gzalles/ambisonics-z-array/cad/dl/screws/M2_Screw_Attempt__3_for_T732_912171/README.txt

M2 Screw Attempt #3 for T732 by Zohan on Thingiverse: https://www.thingiverse.com/thing:912171
