gzalles/ambisonics-z-array/cad/dl/screws/M3_SCREW_WITH_NUT_3730355/README.txt

M3 SCREW WITH NUT by Fern528 on Thingiverse: https://www.thingiverse.com/thing:3730355
