gzalles/ambisonics-z-array/pcb/MEMS_quart_board/40720/3_175mm-radius/misc/full/README.md

this is the gerber files that pcbway made from the .brd file that CM gave me. 
it is a more complete view of the single mems board with 3.175 mm radius
