gzalles/ambisonics-z-array/cad/bigSpHEAR_mems/angles.png

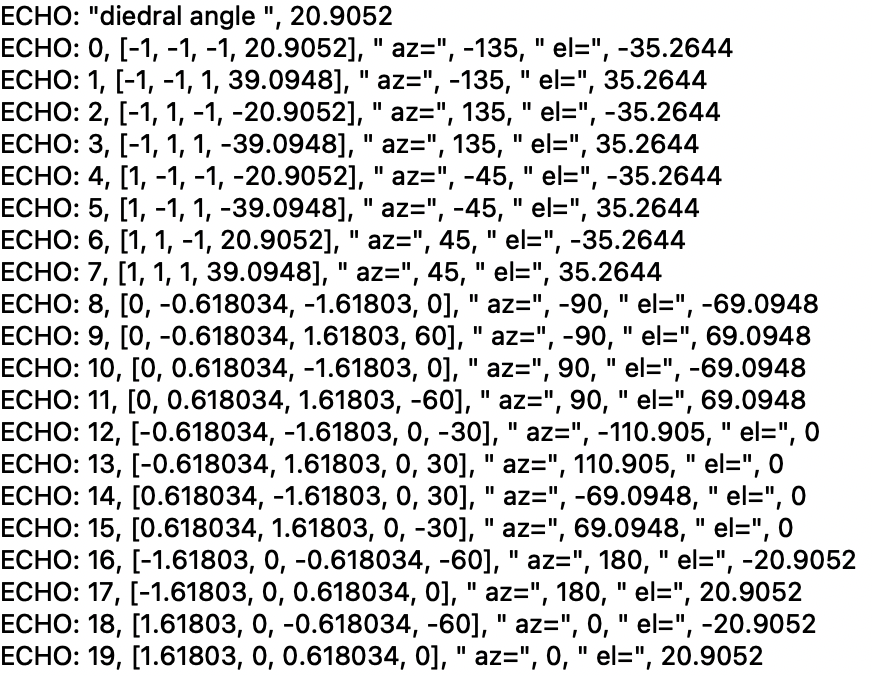
cad/bigSpHEAR_mems/angles.png
