gzalles/ambisonics-z-array/cad/dl/mic-holder/images/Mic_Holder_Samson_Q2U.JPG

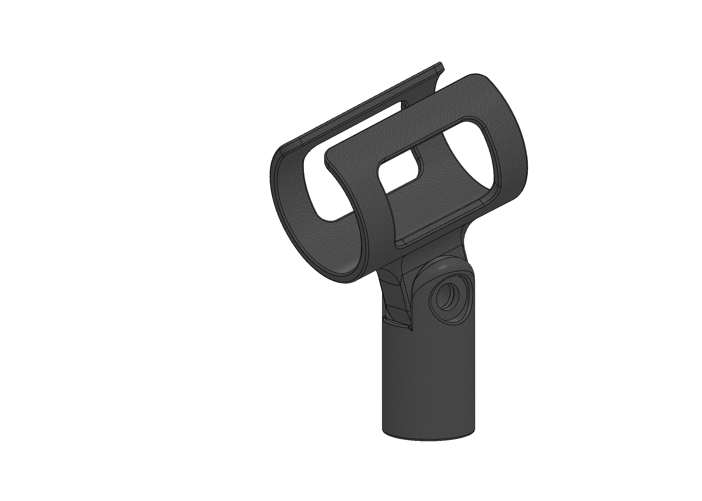
cad/dl/mic-holder/images/Mic_Holder_Samson_Q2U.JPG
