gzalles/ambisonics-z-array/cad/dl/screws/M3_SCREW_WITH_NUT_3730355/images/Capture.JPG

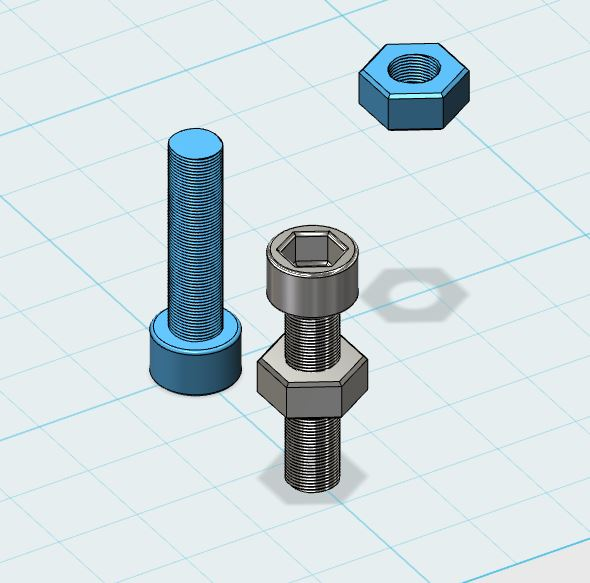
cad/dl/screws/M3_SCREW_WITH_NUT_3730355/images/Capture.JPG
