gzalles/ambisonics-z-array/cad/octo/_angles.png

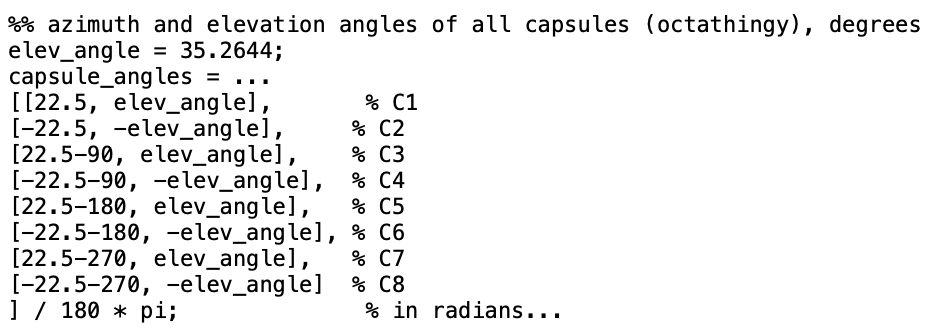
cad/octo/_angles.png
