gzalles/ambisonics-z-array/cad/octo/mch/prusa.png

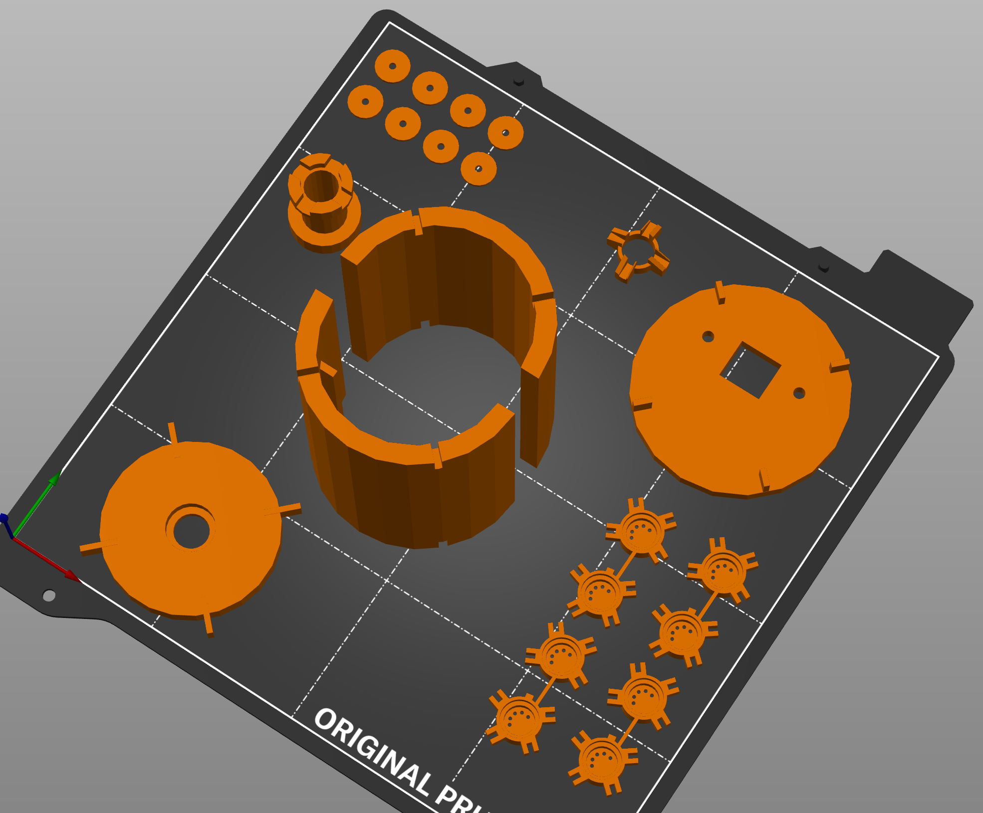
cad/octo/mch/prusa.png
