gzalles/ambisonics-z-array/m/eps/D1/D1-DFRs-AF-local-EQ.jpeg

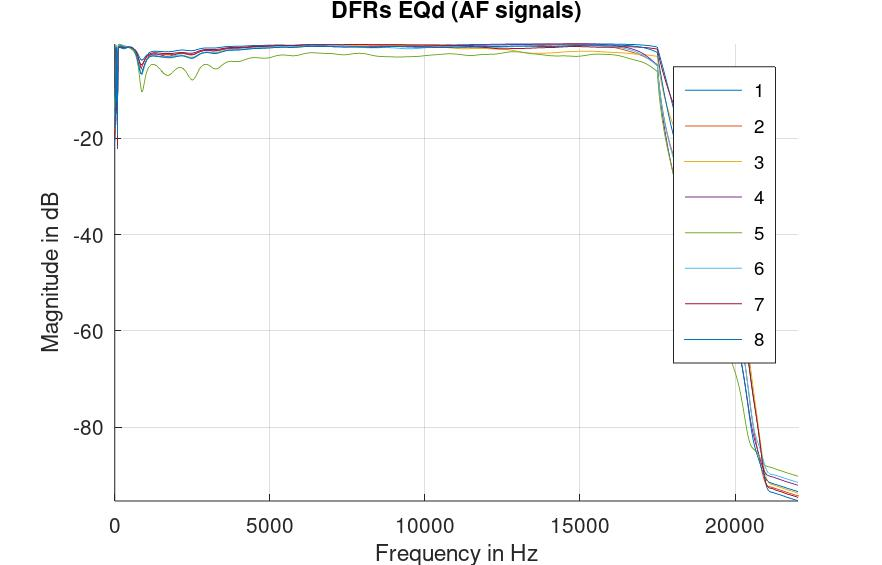
m/eps/D1/D1-DFRs-AF-local-EQ.jpeg
