gzalles/ambisonics-z-array/m/eps/D1/D1-on-axis-preAF-EQ.jpeg

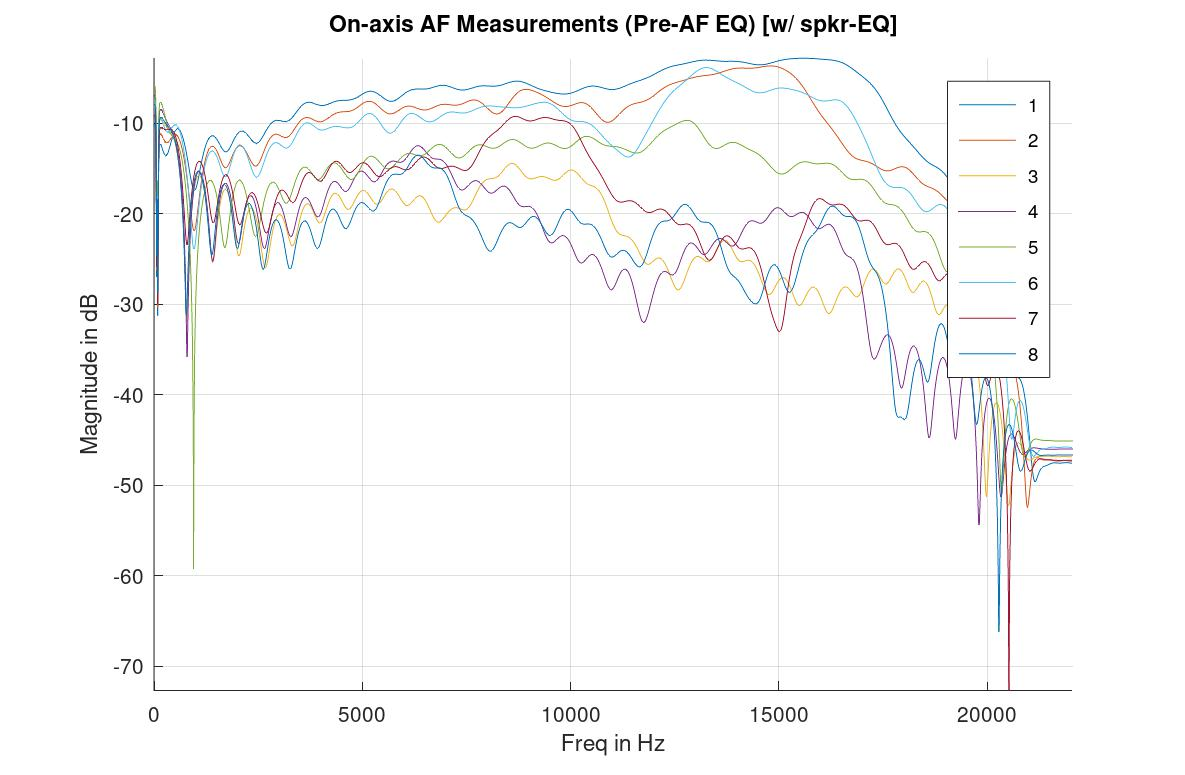
m/eps/D1/D1-on-axis-preAF-EQ.jpeg
