gzalles/ambisonics-z-array/m/eps/D1/D1-SH1-EQ-DFR.jpeg

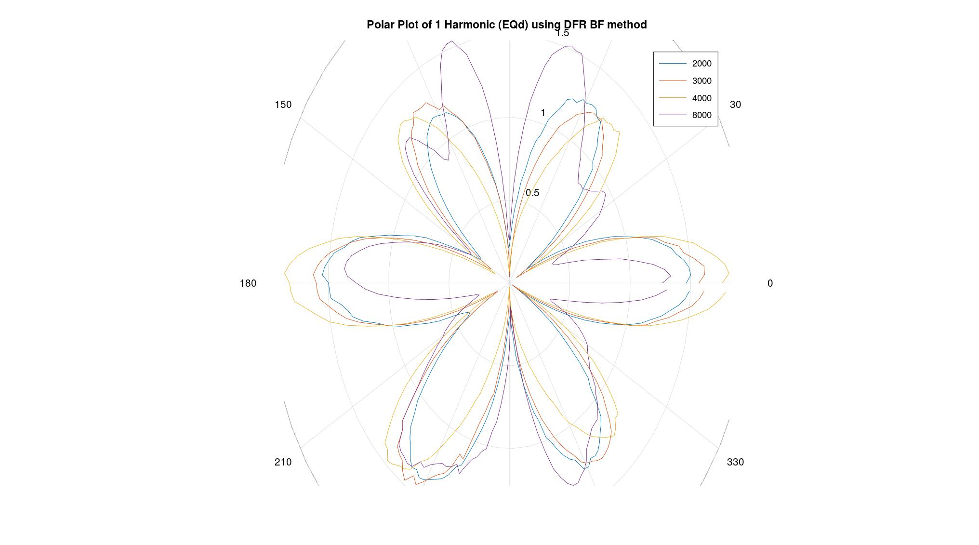
m/eps/D1/D1-SH1-EQ-DFR.jpeg
