gzalles/ambisonics-z-array/m/eps/D1/D1-SH-BF-EQ-peak.jpeg

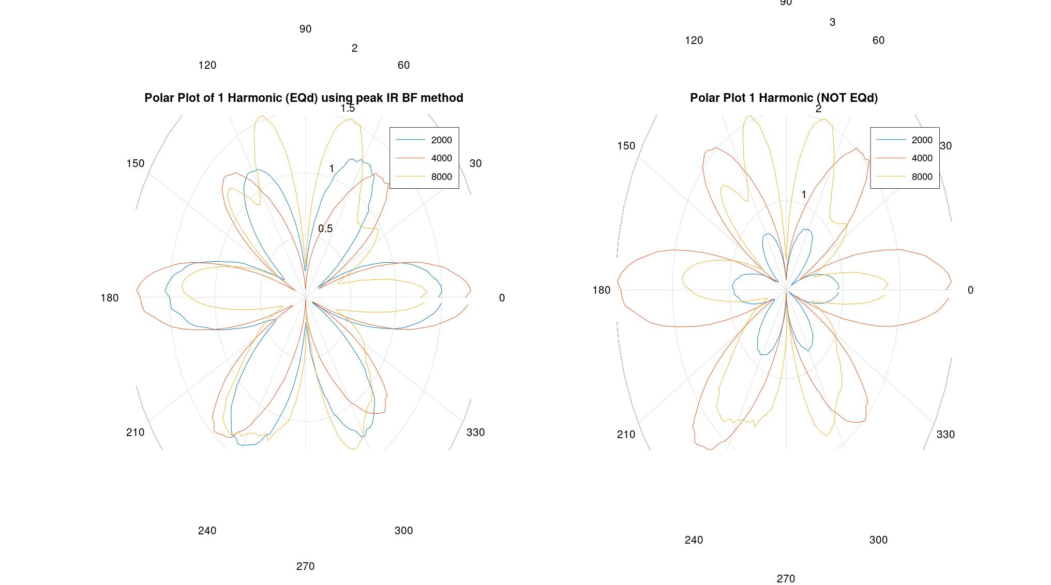
m/eps/D1/D1-SH-BF-EQ-peak.jpeg
