gzalles/ambisonics-z-array/m/eps/D1/D1-SHs-ALL-2k.jpeg

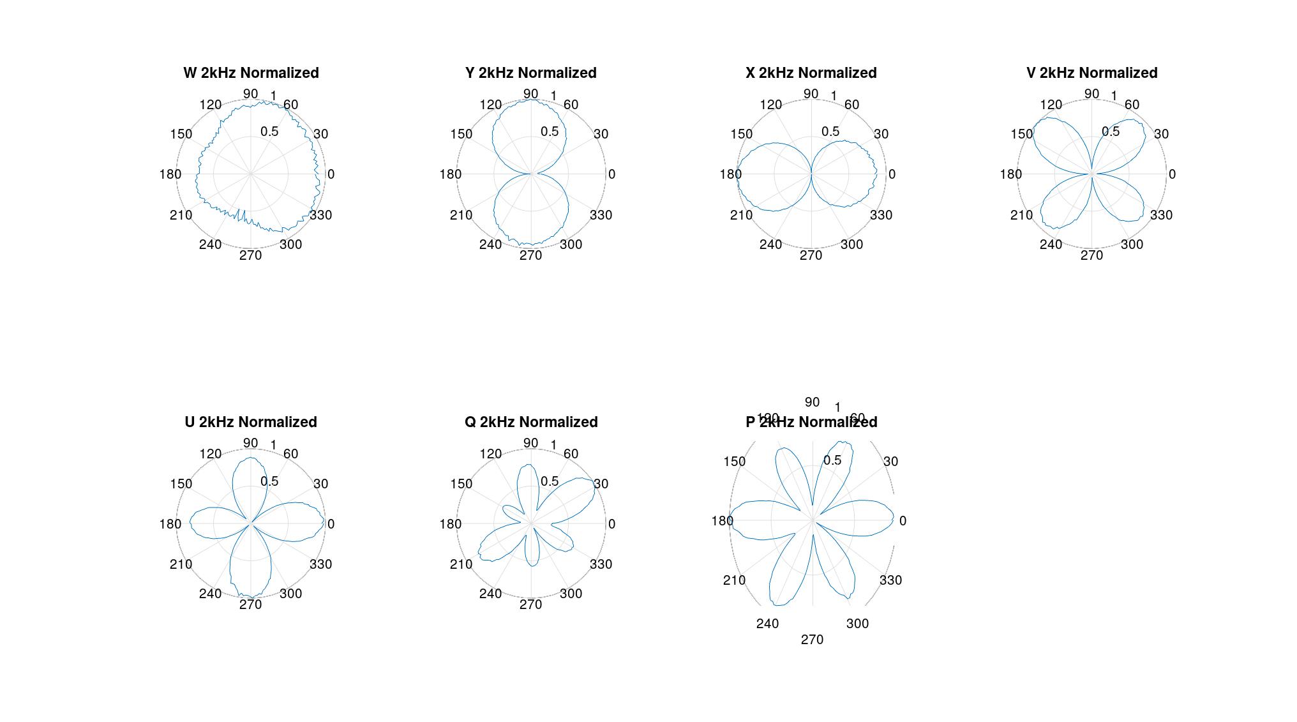
m/eps/D1/D1-SHs-ALL-2k.jpeg
