gzalles/ambisonics-z-array/m/eps/D2/D2-1st-IR-AF-P1-EQ.jpeg

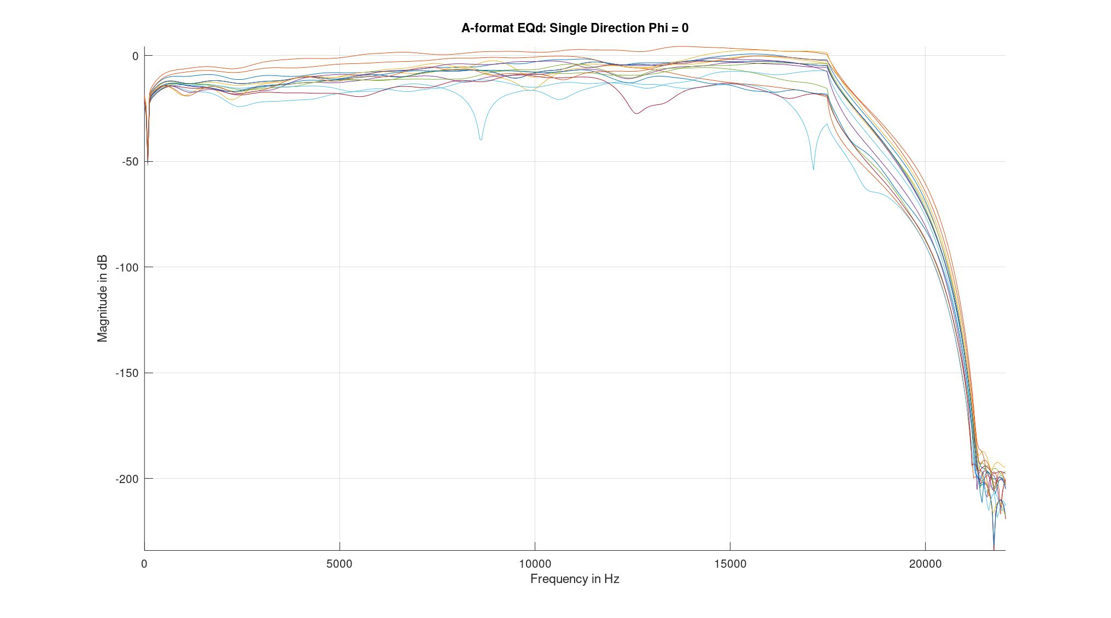
m/eps/D2/D2-1st-IR-AF-P1-EQ.jpeg
