gzalles/ambisonics-z-array/m/eps/D2/D2-SH-ALL-3K.jpeg

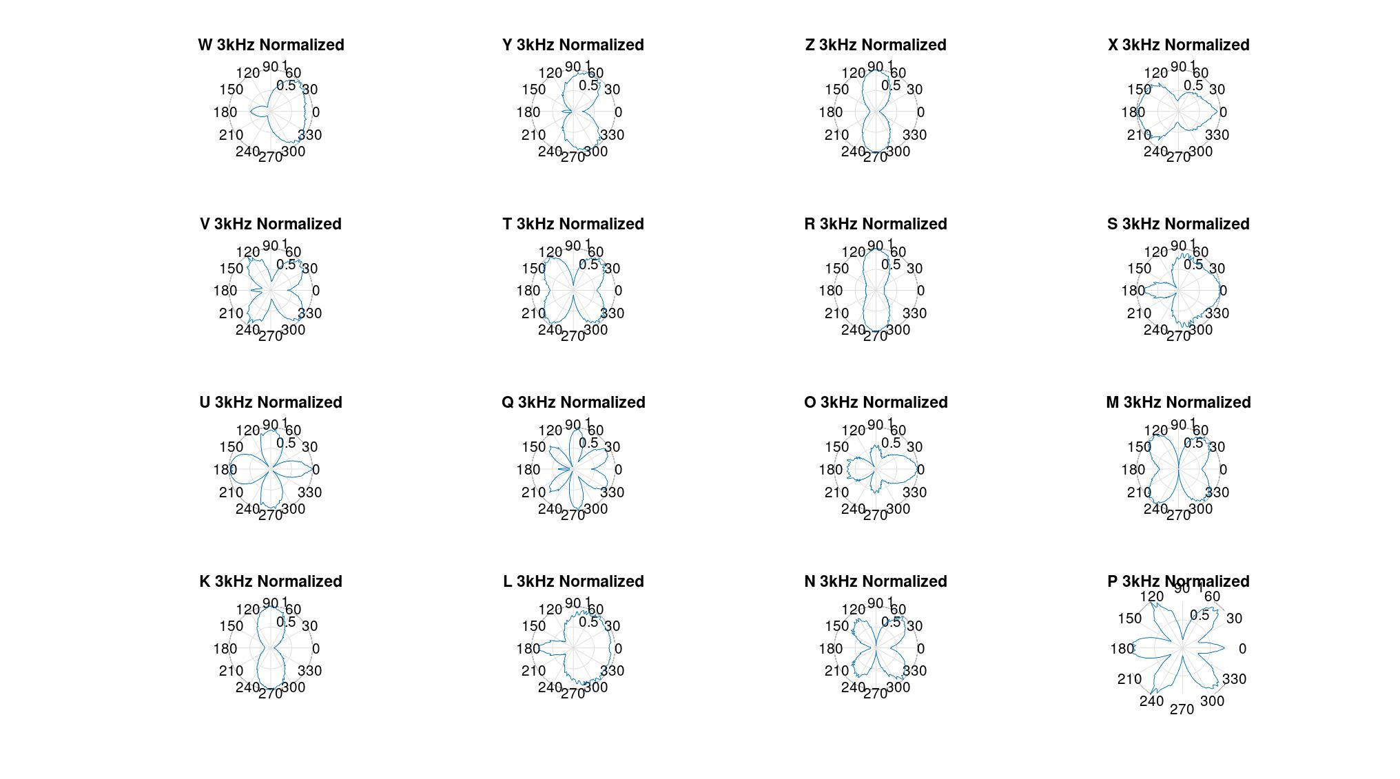
m/eps/D2/D2-SH-ALL-3K.jpeg
