gzalles/ambisonics-z-array/m/eps/D2/D2-SH-ALL-EQ-DFR.jpeg

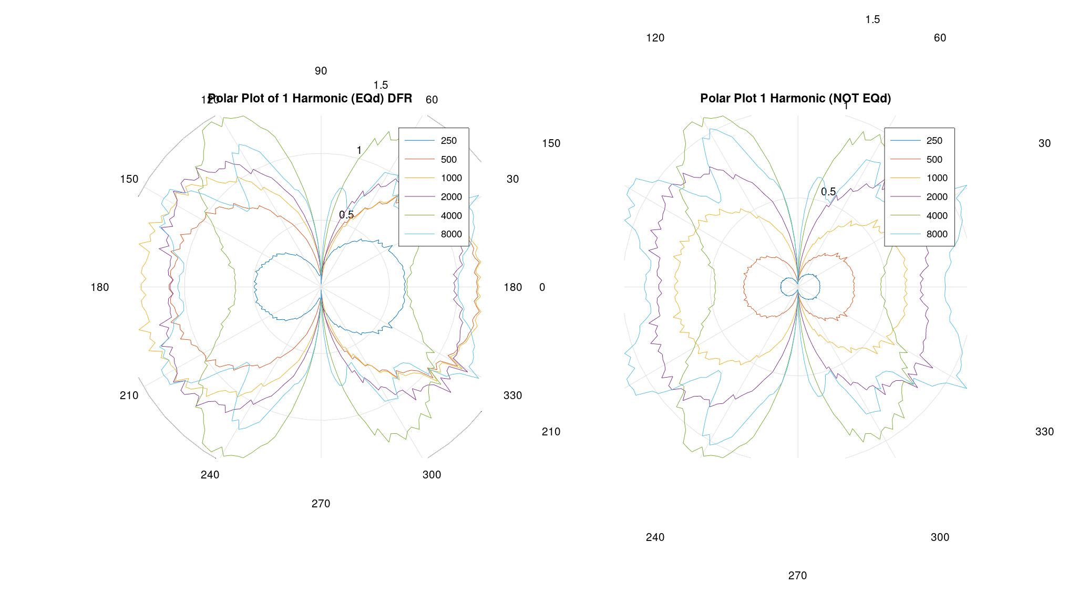
m/eps/D2/D2-SH-ALL-EQ-DFR.jpeg
