gzalles/ambisonics-z-array/pcb/ICS-41350-PDM-Mic-master/dimensions.png

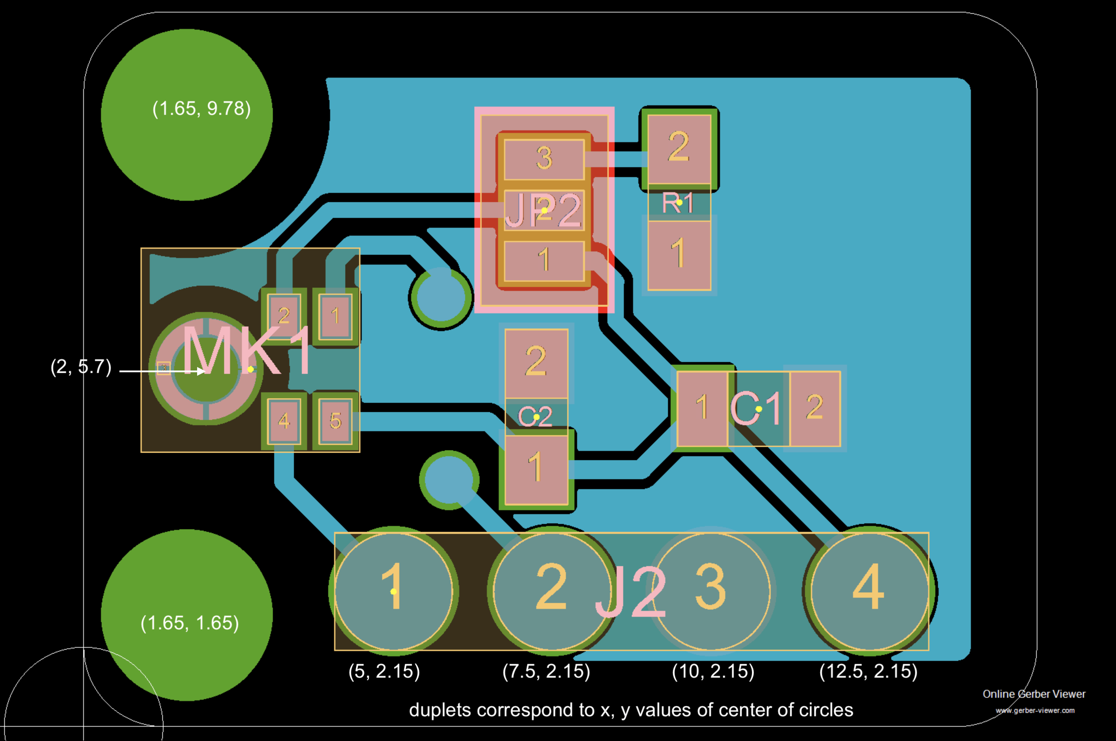
pcb/ICS-41350-PDM-Mic-master/dimensions.png
