gzalles/ambisonics-z-array/pcb/MEMS_quart_board/43432/gerber.png

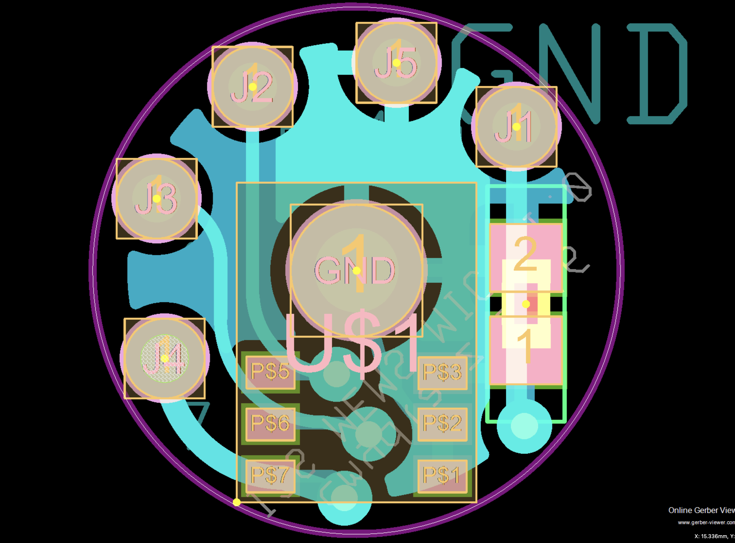
pcb/MEMS_quart_board/43432/gerber.png
