gzalles/ambisonics-z-array/pcb/MEMS_quart_board/43434/gerber2.png

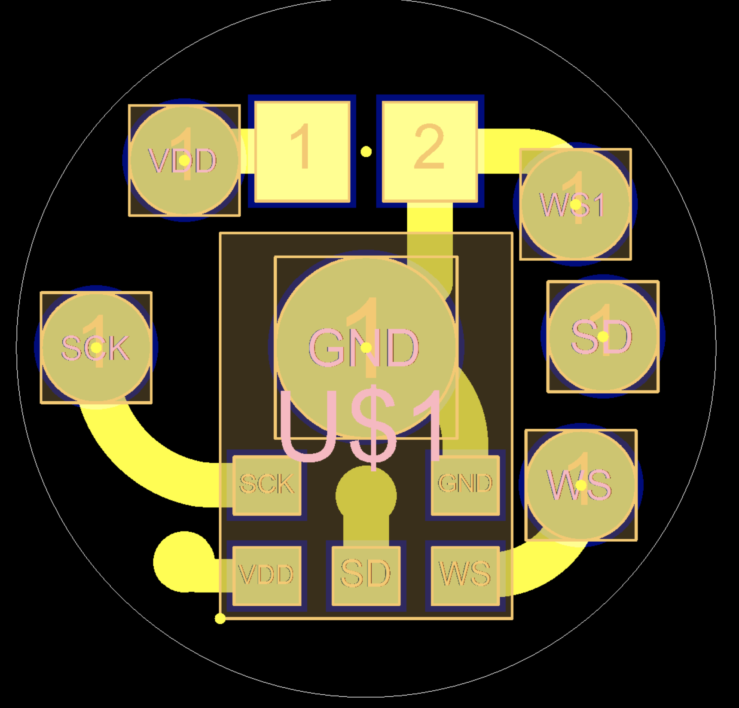
pcb/MEMS_quart_board/43434/gerber2.png
