gzalles/ambisonics-z-array/pcb/MEMS_quart_board/52000/tdm52000-circuit/example1.png

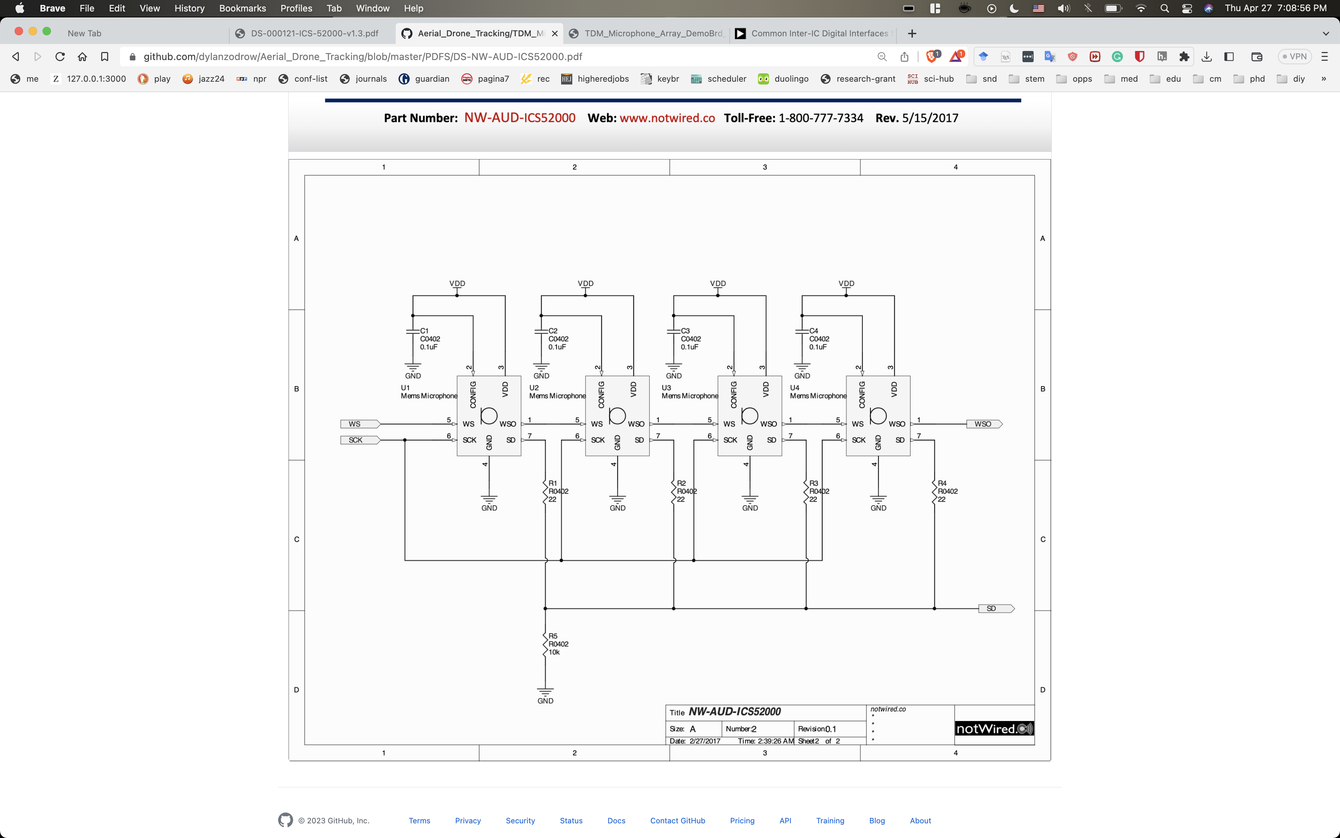
pcb/MEMS_quart_board/52000/tdm52000-circuit/example1.png
