gzalles/ambisonics-z-array/pcb/MEMS_quart_board/SPH0645LM4H/F-RES.png

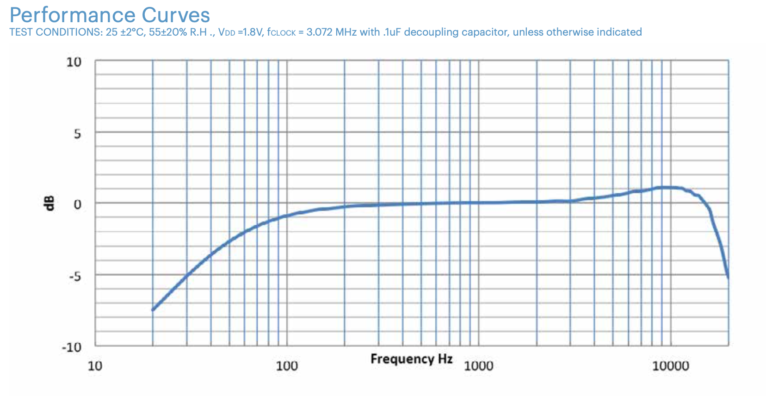
pcb/MEMS_quart_board/SPH0645LM4H/F-RES.png
