gzalles/ambisonics-z-array/cad/dl/scad/gzb/tetrahedron.stl

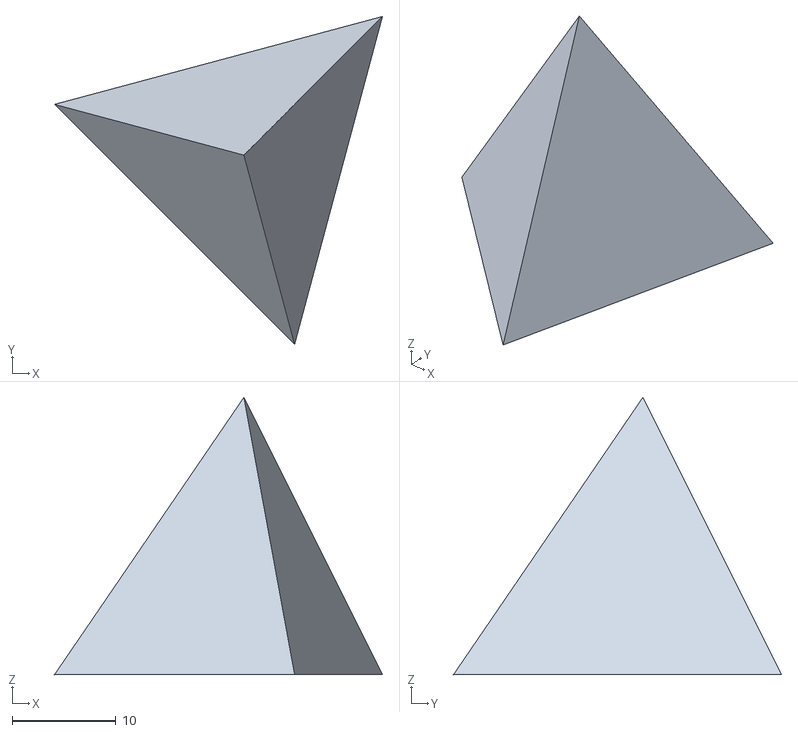
[picture p46: CAD file, 2023-04-07]
cad/dl/scad/gzb/tetrahedron.stl
31.5 x 31.5 x 26.7
