gzalles/ambisonics-z-array/cad/gzb.stl

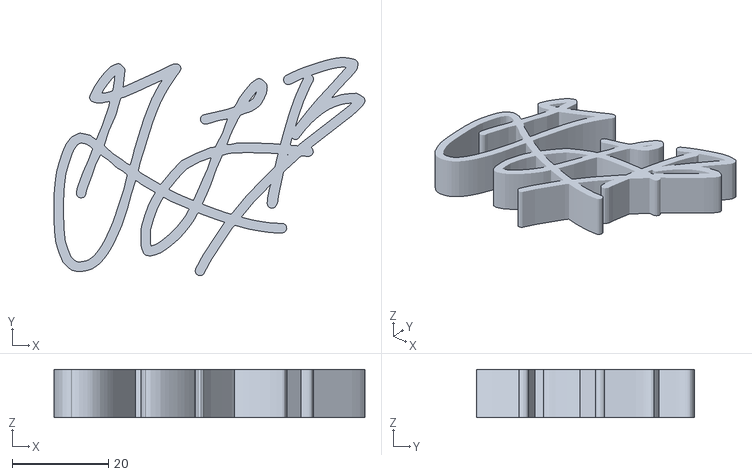
[picture p47: CAD file, 2023-05-23]
cad/gzb.stl
64.6 x 45.3 x 10.0
