gzalles/ambisonics-z-array/cad/max360/83/v2/top.stl

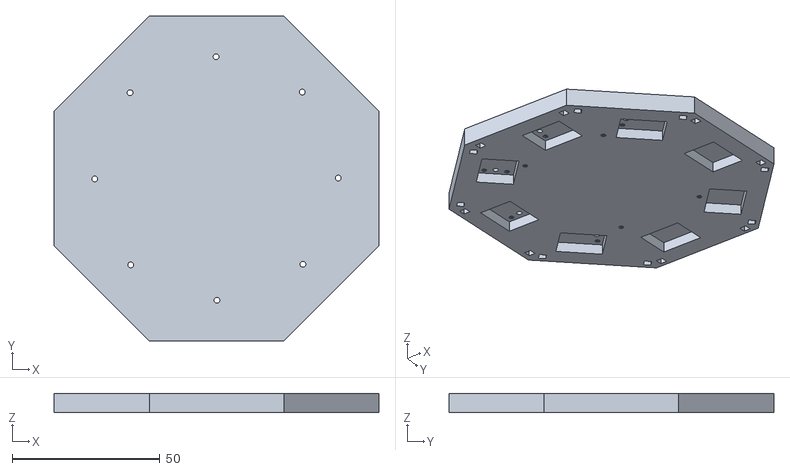
[picture p48: CAD file, 2023-04-07]
cad/max360/83/v2/top.stl
109.9 x 109.9 x 6.59
