gzalles/ambisonics-z-array/cad/max360/ada/2D-I2S-8CH/bottom.3mf

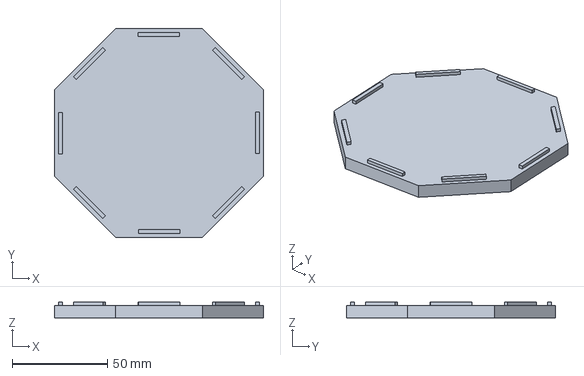
[picture p49: CAD file, 2023-04-07]
cad/max360/ada/2D-I2S-8CH/bottom.3mf
110.0 x 110.0 x 8.24 mm
