gzalles/ambisonics-z-array/cad/max360/ada/2D-I2S-8CH/stl/sides_x7.stl

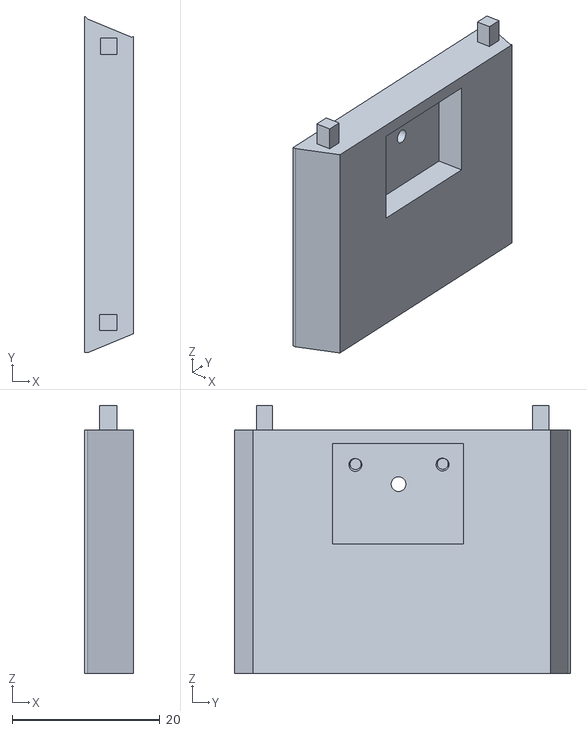
[picture p50: CAD file, 2023-04-07]
cad/max360/ada/2D-I2S-8CH/stl/sides_x7.stl
6.59 x 45.5 x 36.2
