gzalles/ambisonics-z-array/cad/max360/ada/3D-PDM-16CH/sides.3mf

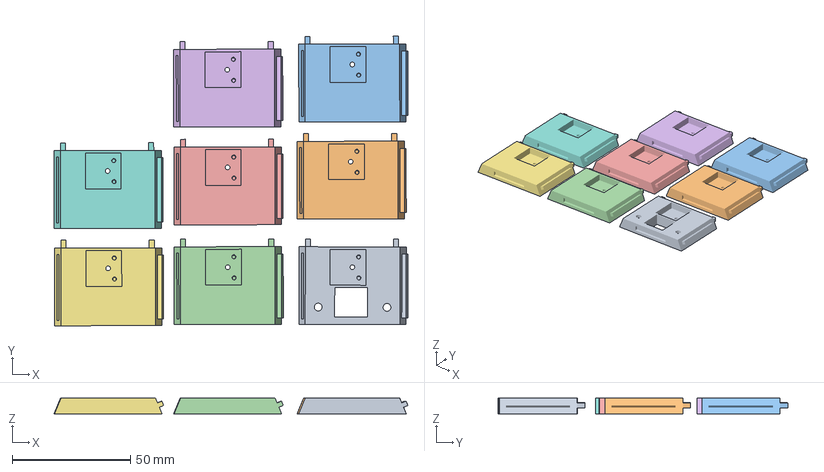
[picture p51: CAD file, 2023-04-07]
cad/max360/ada/3D-PDM-16CH/sides.3mf
149.9 x 122.6 x 6.59 mm
sideA.stl
sideB.stl x 7
