gzalles/ambisonics-z-array/cad/max360/ada/3D-PDM-16CH/stl/sideA.stl

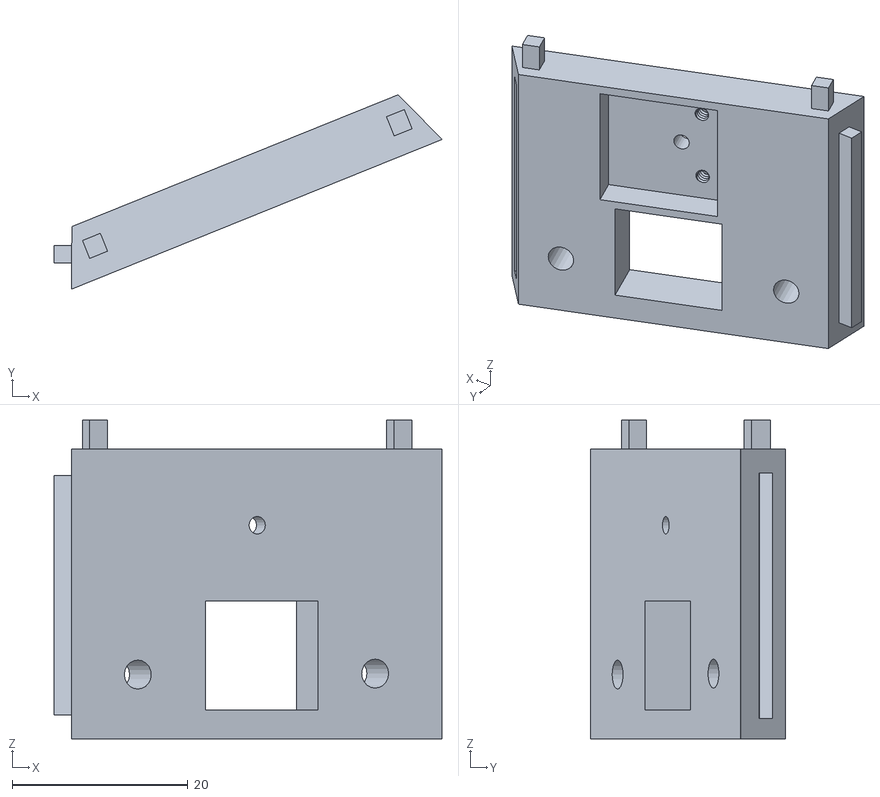
[picture p52: CAD file, 2023-04-07]
cad/max360/ada/3D-PDM-16CH/stl/sideA.stl
44.1 x 22.1 x 36.2
