gzalles/ambisonics-z-array/cad/msma-mch/capHolder16-new.3mf

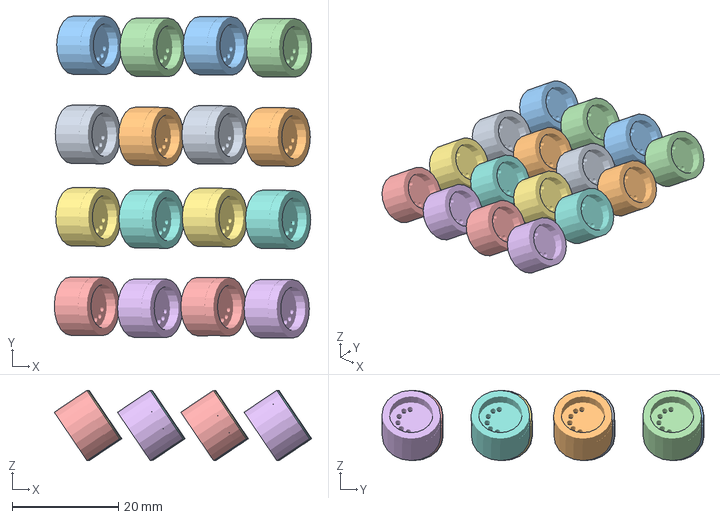
[picture p53: CAD file, 2023-04-19]
cad/msma-mch/capHolder16-new.3mf
48.5 x 60.7 x 13.2 mm
capHolder16-new.stl x 16
