gzalles/ambisonics-z-array/cad/octo/mch/neck.stl

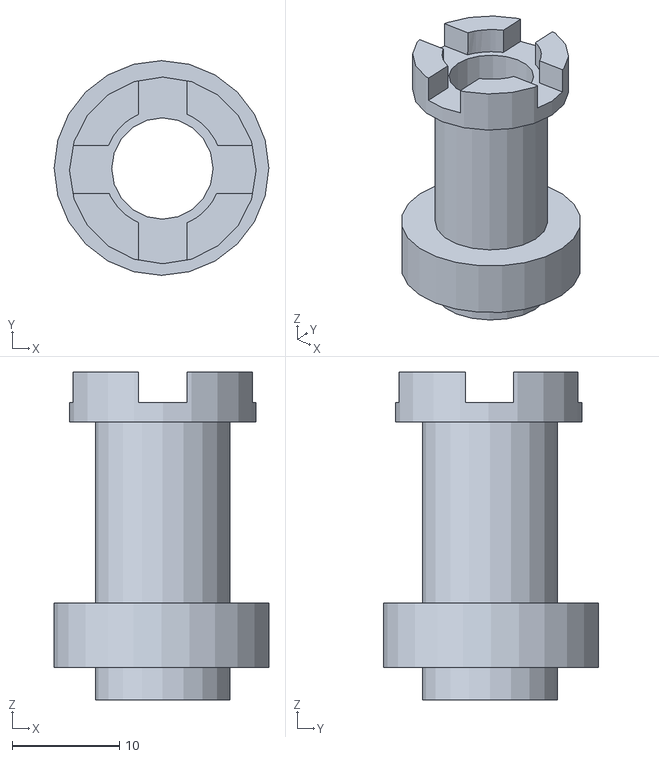
[picture p54: CAD file, 2023-04-07]
cad/octo/mch/neck.stl
20.0 x 20.0 x 30.5
