gzalles/ambisonics-z-array/cad/octo/mch/prusa/sides.3mf

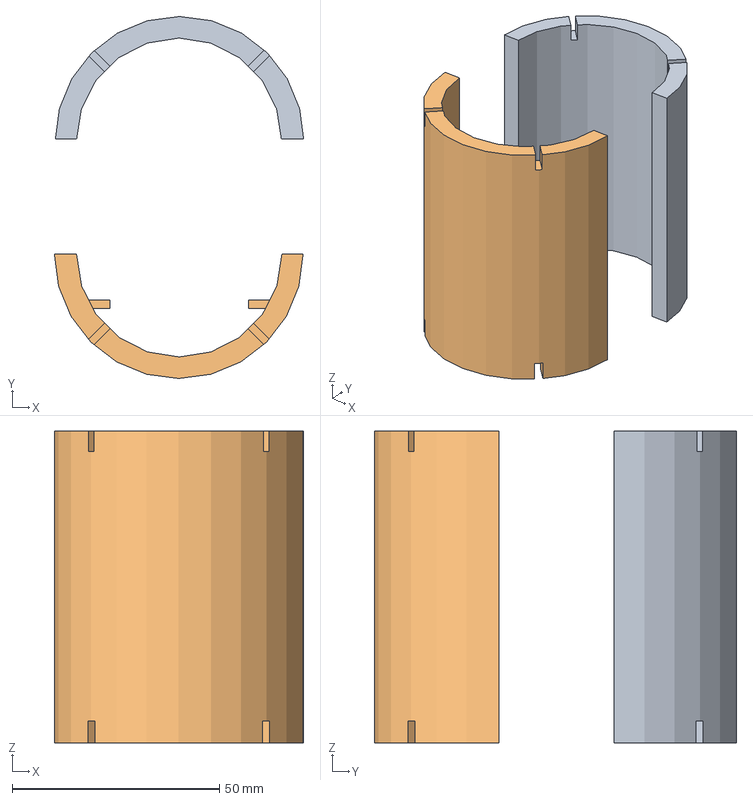
[picture p55: CAD file, 2023-04-07]
cad/octo/mch/prusa/sides.3mf
60.1 x 87.3 x 75.1 mm
side-a.stl
side-b.stl
