gzalles/ambisonics-z-array/cad/tiny/TinySpHEAR_top.stl

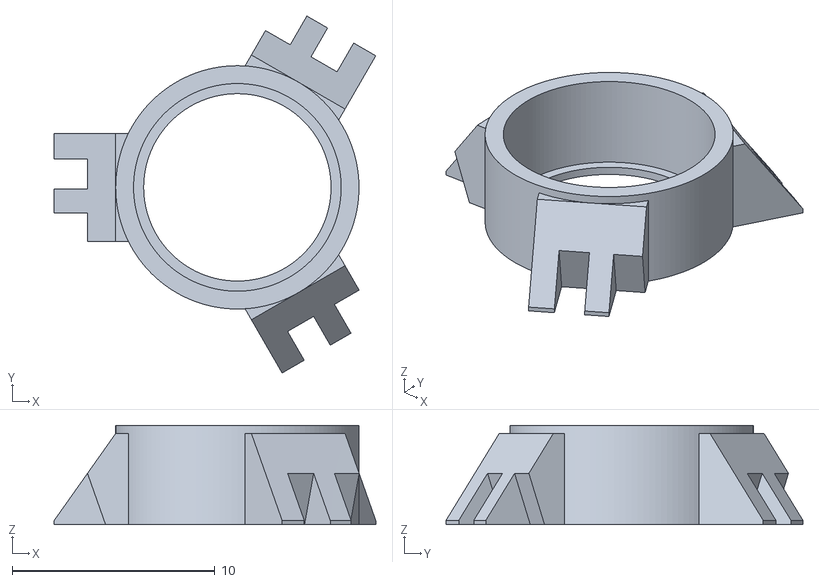
[picture p56: CAD file, 2023-04-07]
cad/tiny/TinySpHEAR_top.stl
15.9 x 17.6 x 4.90
