gzalles/ambisonics-z-array/cad/_temp/missing/2/neck.stl

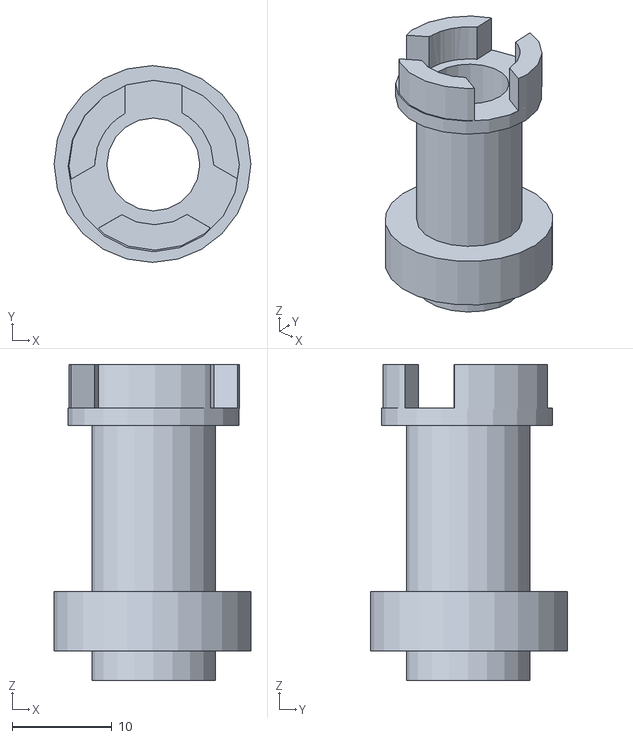
[picture p57: CAD file, 2023-04-07]
cad/_temp/missing/2/neck.stl
19.8 x 19.8 x 31.7
