gzalles/ambisonics-z-array/cad/_temp/missing/3/side-b.stl

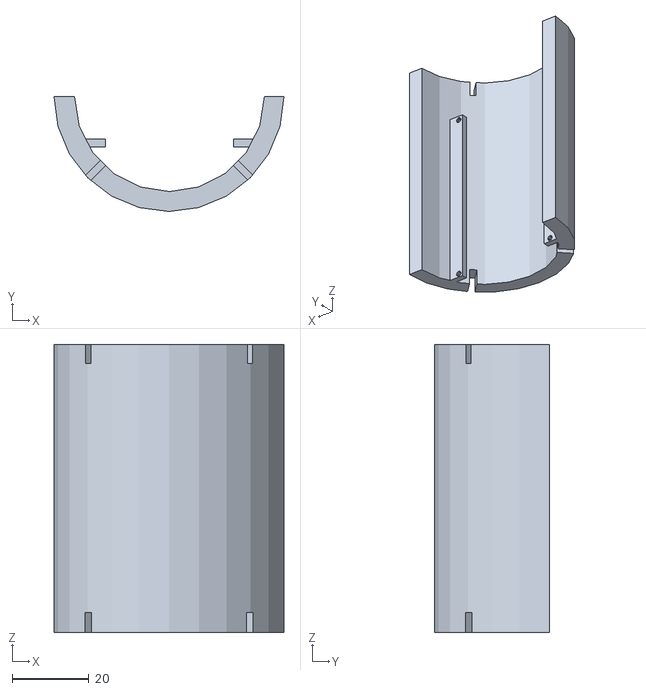
[picture p58: CAD file, 2023-04-07]
cad/_temp/missing/3/side-b.stl
60.0 x 30.0 x 75.1
