gzalles/ambisonics-z-array/cad/_temp/missing/4/sideB.stl

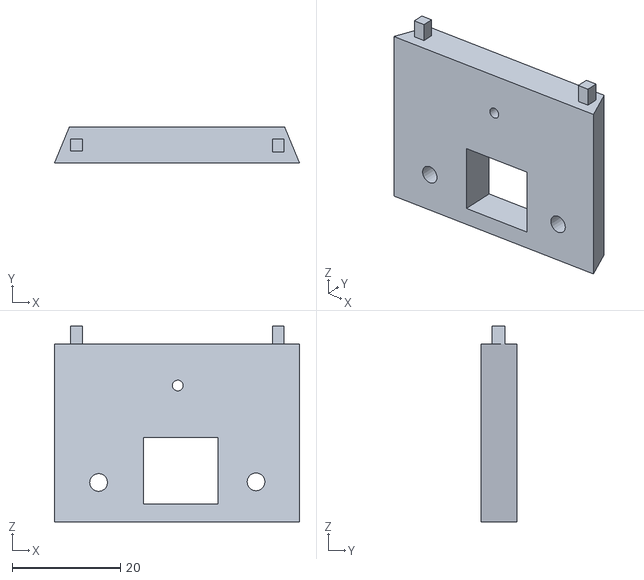
[picture p59: CAD file, 2023-04-07]
cad/_temp/missing/4/sideB.stl
45.3 x 6.59 x 36.2
