gzalles/ambisonics-z-array/cad/bigSpHEAR_mems/big-3d-printed/empty-cap-holder.stl

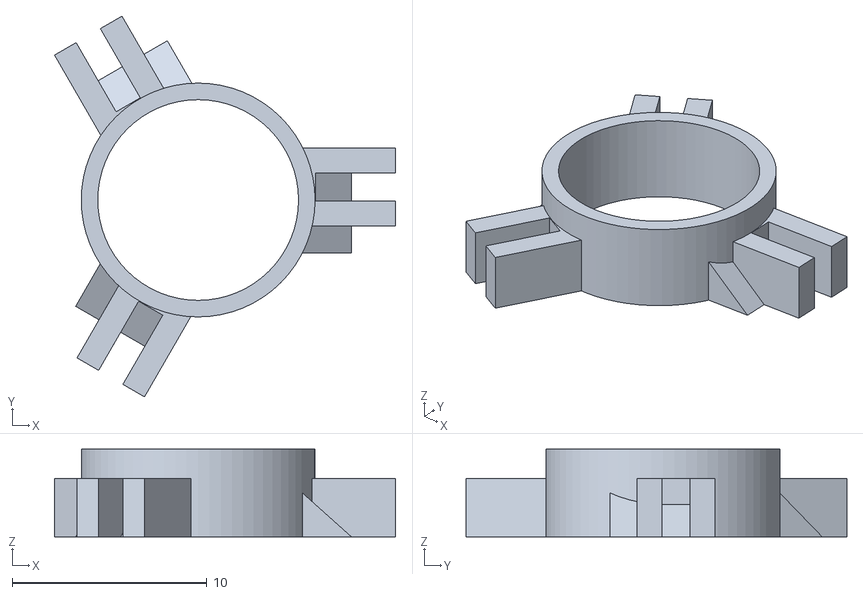
[picture p60: CAD file, 2023-04-07]
cad/bigSpHEAR_mems/big-3d-printed/empty-cap-holder.stl
17.5 x 19.5 x 4.50
