gzalles/ambisonics-z-array/cad/bigSpHEAR_mems/big-3d-printed/gcode/big-3d-printed.3mf

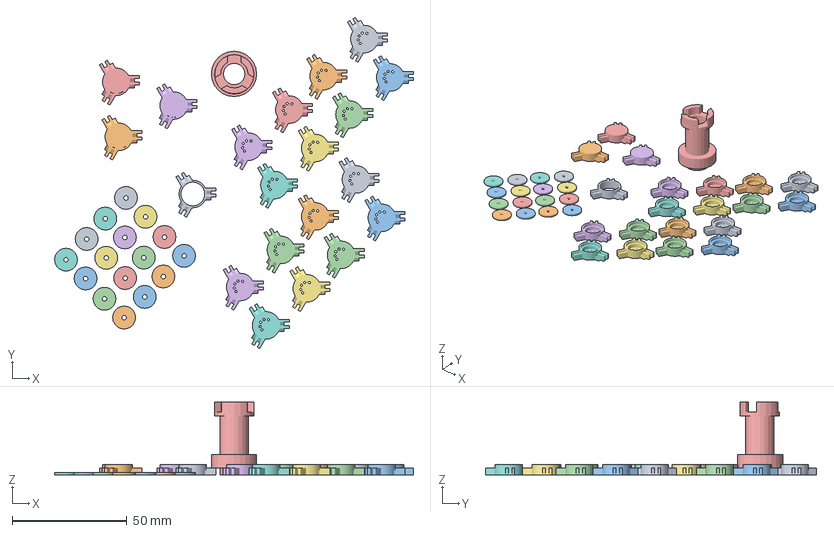
[picture p61: CAD file, 2023-04-07]
cad/bigSpHEAR_mems/big-3d-printed/gcode/big-3d-printed.3mf
156.3 x 144.2 x 31.7 mm
empty-cap-holder.stl
filled-cap-holder.stl x 3
lid.stl x 17
main-cap-holder.stl x 16
neck.stl
