gzalles/ambisonics-z-array/cad/bigSpHEAR_mems/big-3d-printed/gcode/SLS/big-3d-printed-SLS.3mf

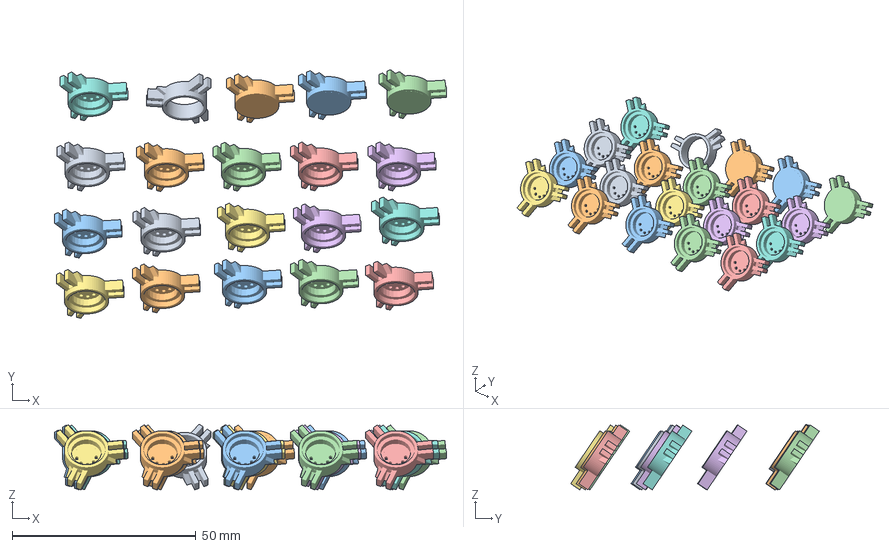
[picture p62: CAD file, 2023-04-07]
cad/bigSpHEAR_mems/big-3d-printed/gcode/SLS/big-3d-printed-SLS.3mf
106.6 x 67.6 x 17.9 mm
main-cap-holder.stl x 16
empty-cap-holder.stl
filled-cap-holder.stl x 3
