gzalles/ambisonics-z-array/cad/bigSpHEAR_mems/BigSpHEAR_20_single_noRamp.stl

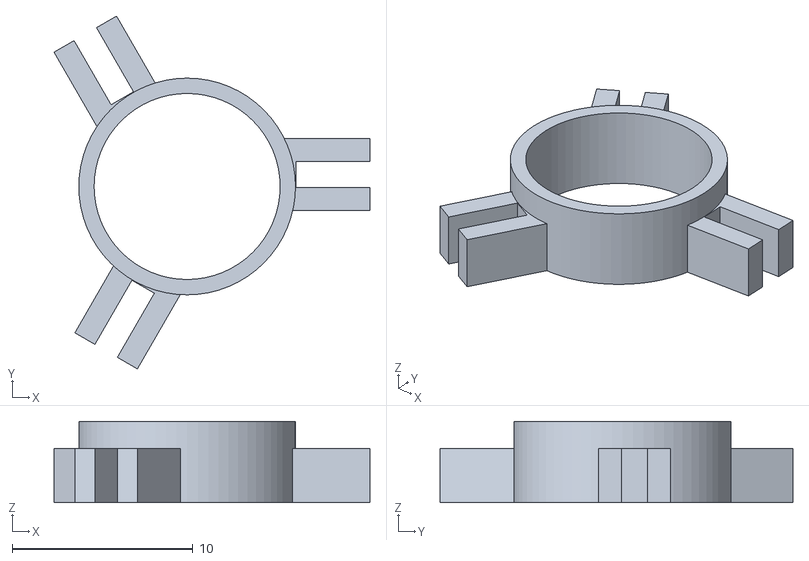
[picture p63: CAD file, 2023-04-07]
cad/bigSpHEAR_mems/BigSpHEAR_20_single_noRamp.stl
17.5 x 19.5 x 4.50
