gzalles/ambisonics-z-array/cad/dl/mic-holder/files/Mic_Holder_Standard_Size.STL

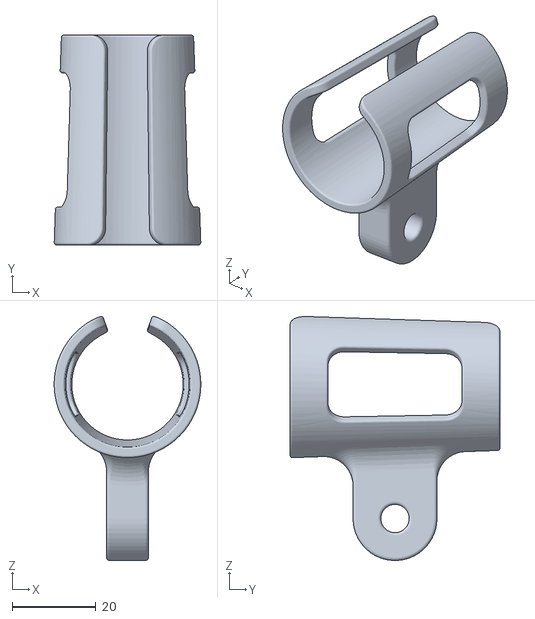
[picture p64: CAD file, 2023-04-07]
cad/dl/mic-holder/files/Mic_Holder_Standard_Size.STL
35.0 x 50.0 x 58.2
