gzalles/ambisonics-z-array/cad/dl/mic-thread.stl

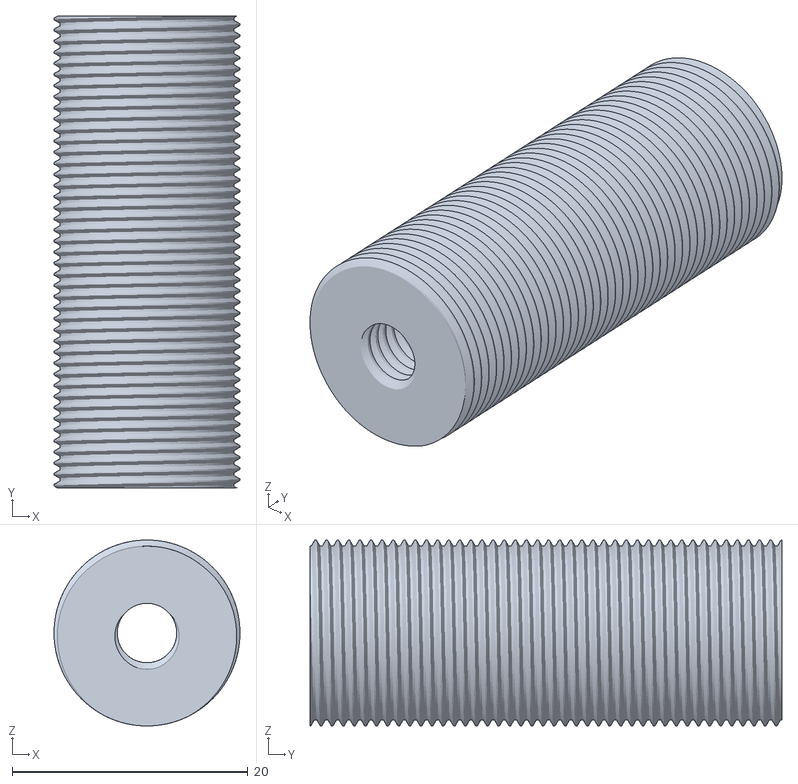
[picture p65: CAD file, 2023-04-07]
cad/dl/mic-thread.stl
15.8 x 40.0 x 15.8
