gzalles/ambisonics-z-array/cad/dl/msma/Mic Head.stl

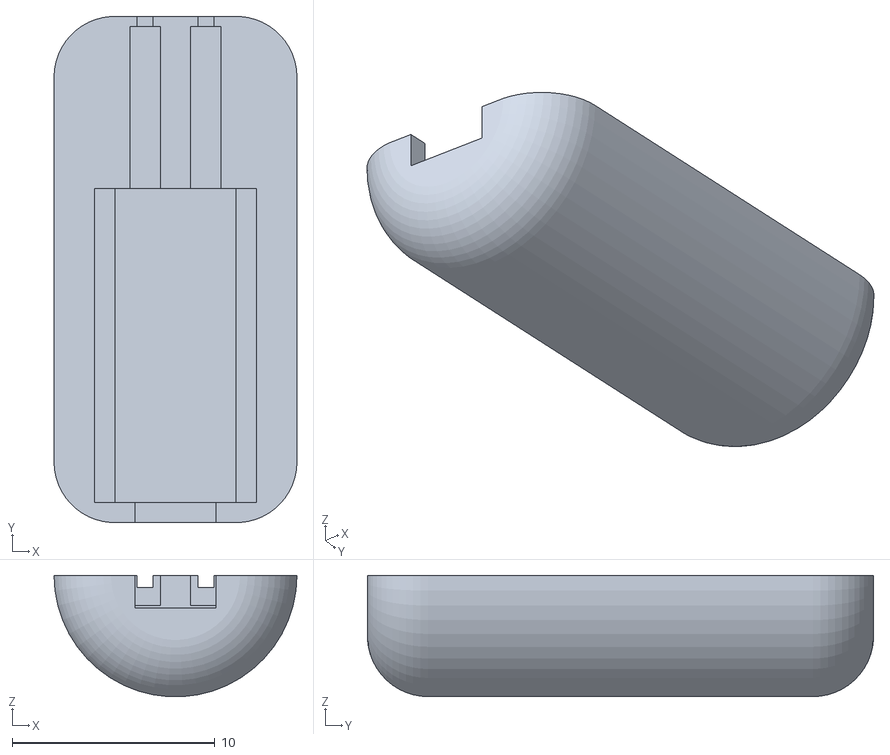
[picture p66: CAD file, 2023-04-07]
cad/dl/msma/Mic Head.stl
12.0 x 25.0 x 5.99
