gzalles/ambisonics-z-array/cad/max360/ada/2D-I2S-8CH/top.3mf

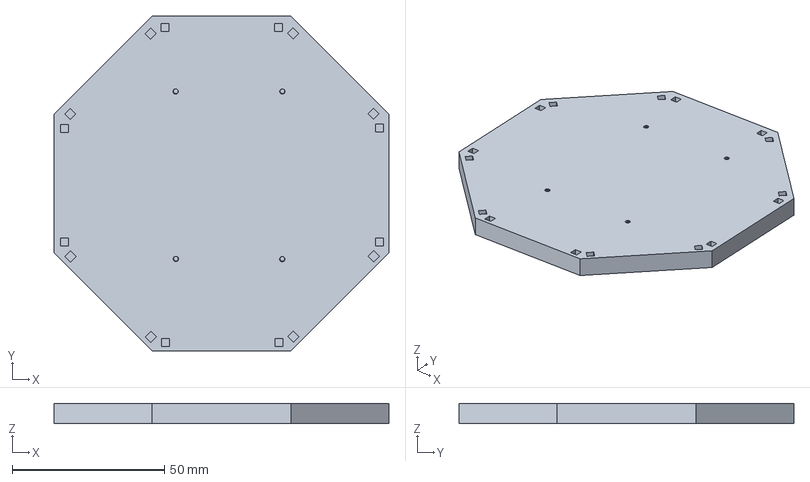
[picture p67: CAD file, 2023-04-07]
cad/max360/ada/2D-I2S-8CH/top.3mf
109.9 x 109.8 x 6.59 mm
