gzalles/ambisonics-z-array/cad/max360/ada/2D-PDM-16CH/bottom.stl

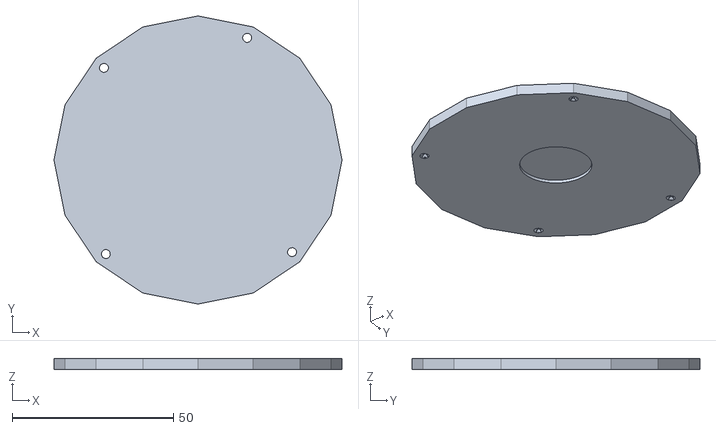
[picture p68: CAD file, 2023-05-23]
cad/max360/ada/2D-PDM-16CH/bottom.stl
89.2 x 89.2 x 3.37
