gzalles/ambisonics-z-array/cad/max360/ada/3D-PDM-16CH/max360-ADA.3mf

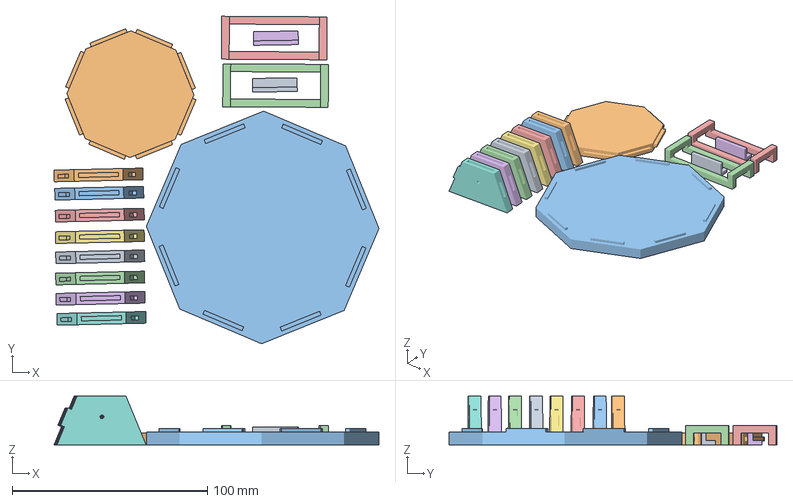
[picture p69: CAD file, 2023-04-07]
cad/max360/ada/3D-PDM-16CH/max360-ADA.3mf
166.3 x 167.6 x 24.9 mm
perf-board-holder.stl x 2
top-single.stl x 8
top-center.stl
bottom.stl
bracket.stl x 2
