gzalles/ambisonics-z-array/cad/max360/ada/3D-PDM-16CH/stl/bracket.stl

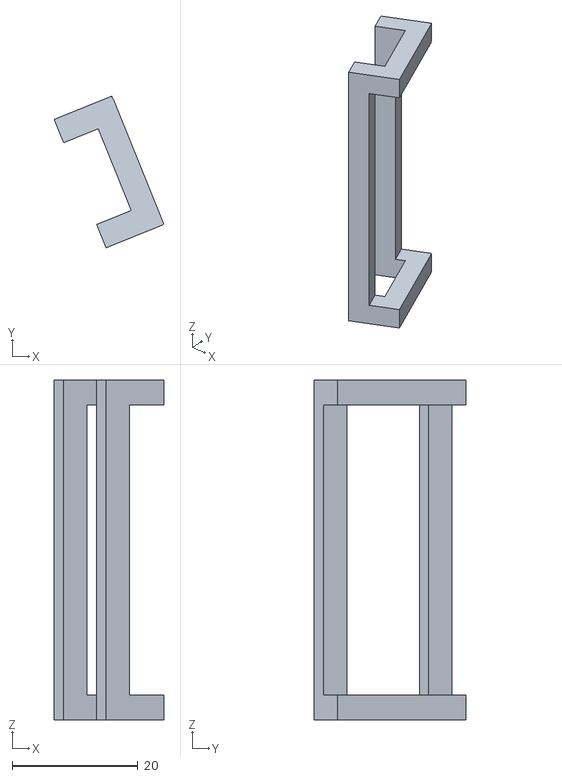
[picture p70: CAD file, 2023-04-07]
cad/max360/ada/3D-PDM-16CH/stl/bracket.stl
17.4 x 24.1 x 54.0
