gzalles/ambisonics-z-array/cad/msma-mch/neck.stl

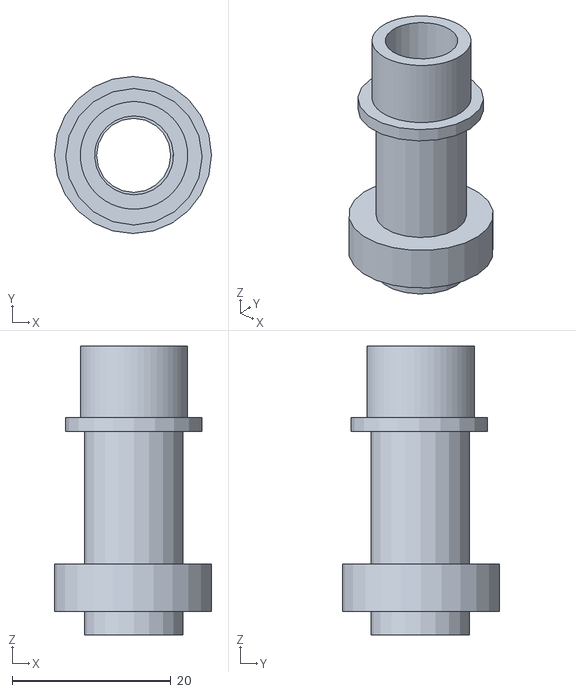
[picture p71: CAD file, 2023-04-07]
cad/msma-mch/neck.stl
19.8 x 19.8 x 36.4
