gzalles/ambisonics-z-array/cad/octo/mch/lid.stl

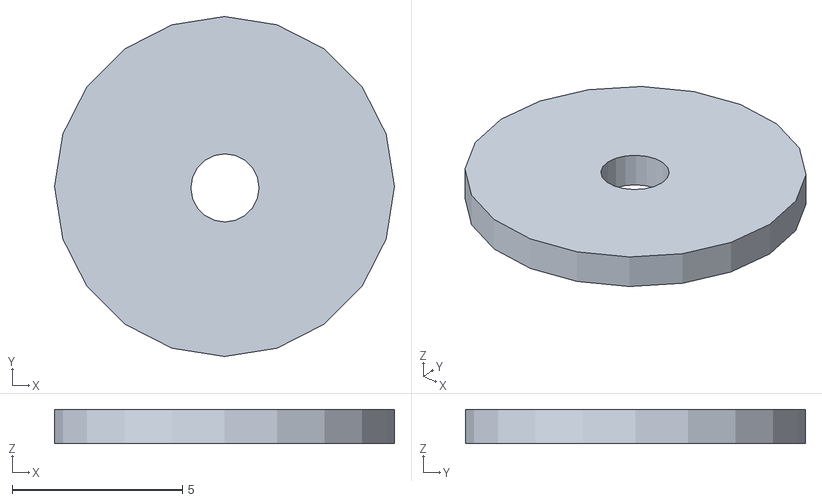
[picture p72: CAD file, 2023-04-07]
cad/octo/mch/lid.stl
10.0 x 10.0 x 1.00
