gzalles/ambisonics-z-array/cad/octo/mch/prusa/no_sides.3mf

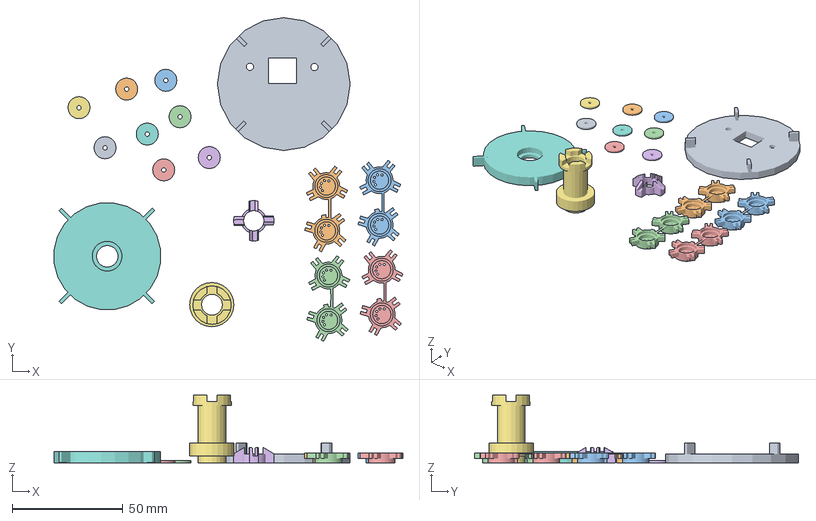
[picture p73: CAD file, 2023-04-07]
cad/octo/mch/prusa/no_sides.3mf
157.6 x 146.2 x 30.5 mm
bottom.stl
cap-holder.stl x 4
connector.stl
lid.stl x 8
neck.stl
top.stl
