gzalles/ambisonics-z-array/cad/tiny/TinySpHEAR_EM182.stl

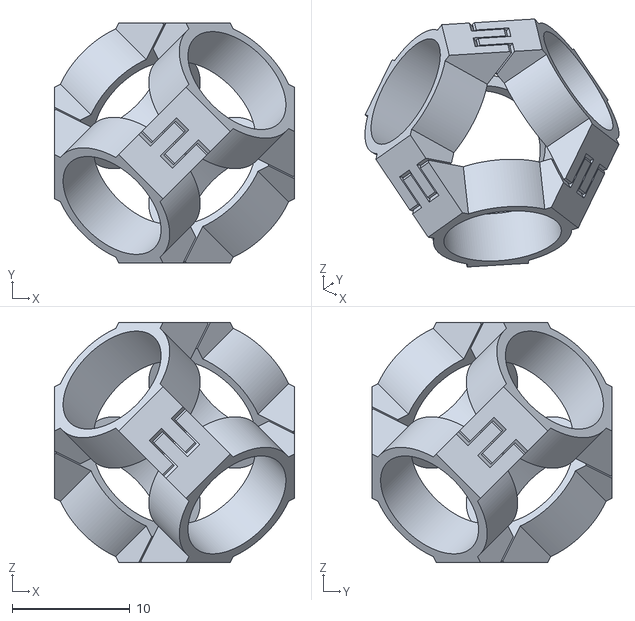
[picture p74: CAD file, 2023-04-07]
cad/tiny/TinySpHEAR_EM182.stl
20.4 x 20.4 x 20.4
