gzalles/ambisonics-z-array/cad/bigSpHEAR_mems/big-3d-printed/cpy/side-a.stl

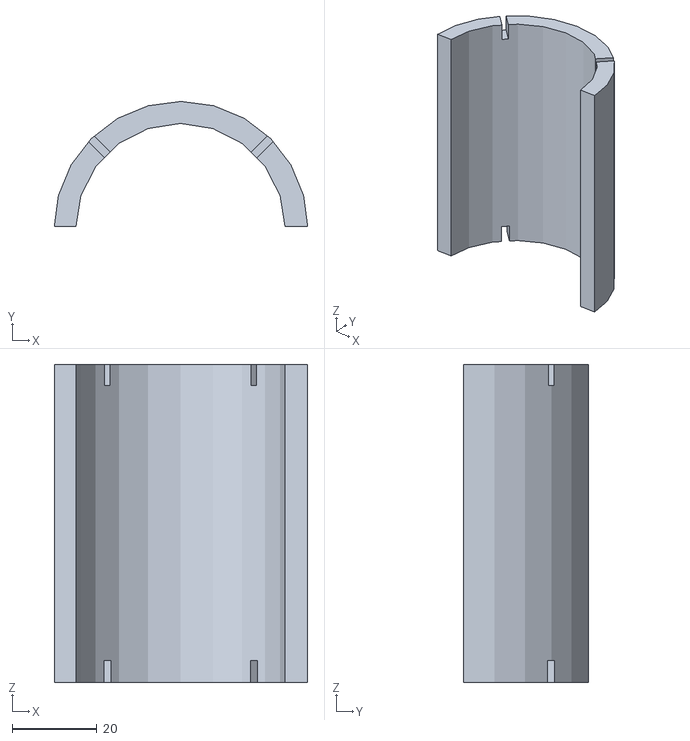
[picture p75: CAD file, 2023-04-07]
cad/bigSpHEAR_mems/big-3d-printed/cpy/side-a.stl
59.9 x 29.6 x 75.1
