gzalles/ambisonics-z-array/cad/dl/icosa.stl

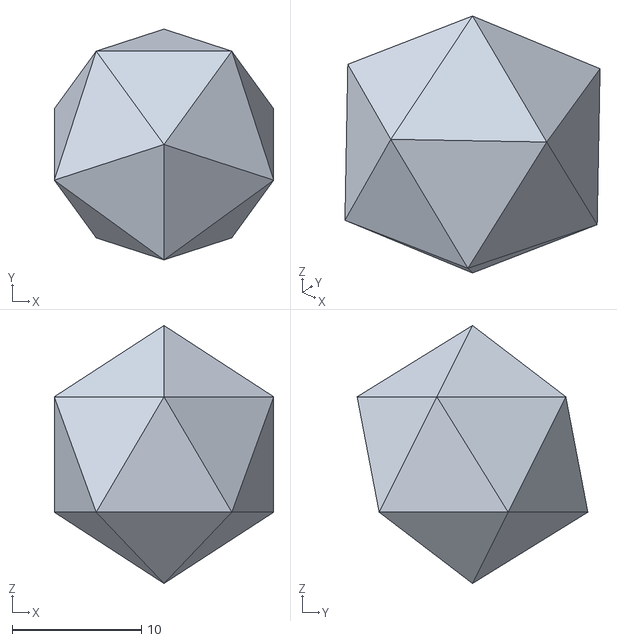
[picture p77: CAD file, 2023-04-07]
cad/dl/icosa.stl
17.0 x 17.9 x 20.0
