gzalles/ambisonics-z-array/cad/dl/mic-holder/files/Stand_Mount.STL

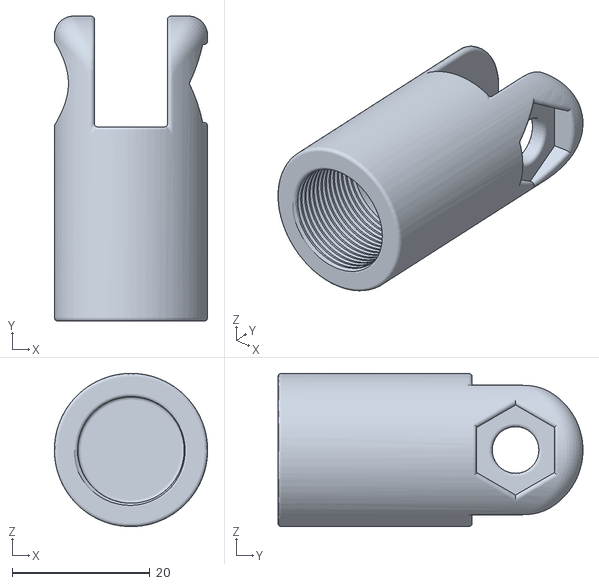
[picture p78: CAD file, 2023-04-07]
cad/dl/mic-holder/files/Stand_Mount.STL
22.2 x 44.2 x 22.2
