gzalles/ambisonics-z-array/cad/dl/msma/Core B.stl

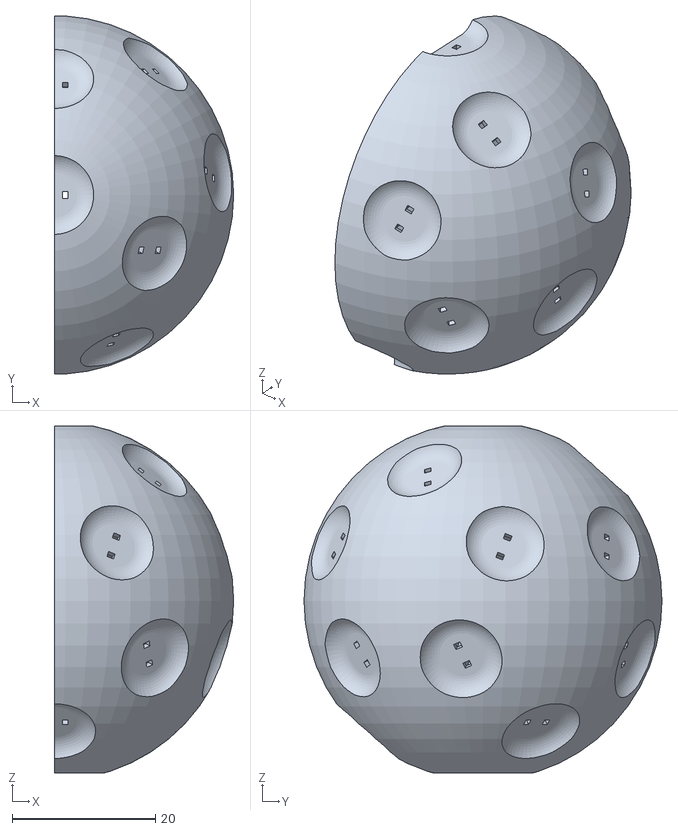
[picture p79: CAD file, 2023-04-07]
cad/dl/msma/Core B.stl
25.0 x 49.9 x 48.3
