gzalles/ambisonics-z-array/cad/max360/ada/2D-I2S-8CH/no_top_or_bottom.3mf

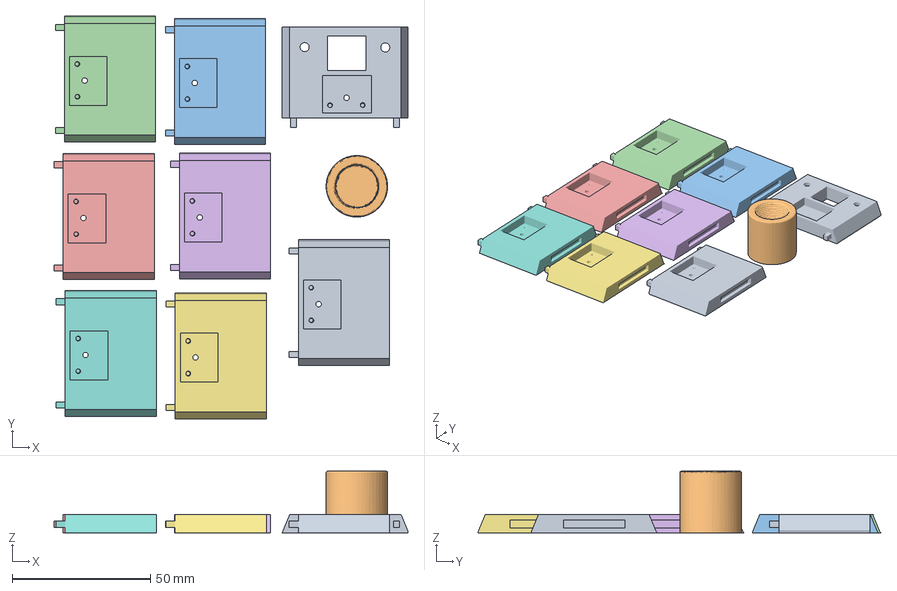
[picture p80: CAD file, 2023-04-07]
cad/max360/ada/2D-I2S-8CH/no_top_or_bottom.3mf
127.9 x 145.5 x 22.3 mm
back.stl
mic_adapter.stl
sides_x7.stl x 7
