gzalles/ambisonics-z-array/cad/max360/ada/2D-PDM-16CH/body.stl

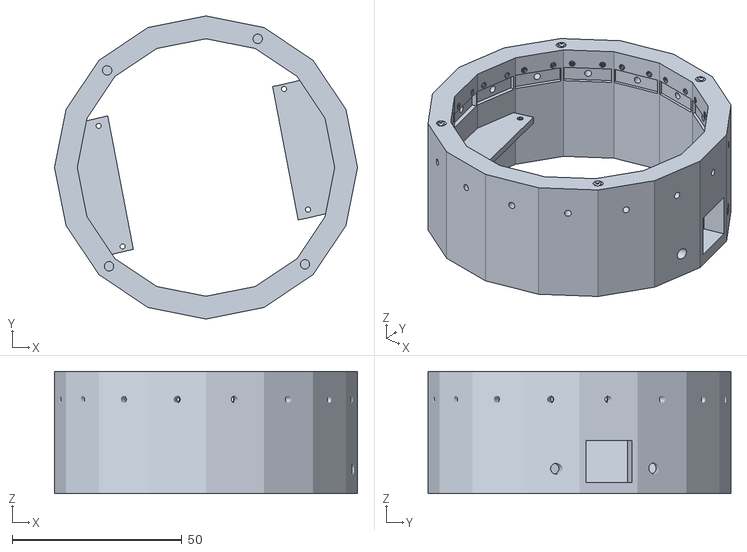
[picture p81: CAD file, 2023-05-23]
cad/max360/ada/2D-PDM-16CH/body.stl
89.2 x 89.2 x 35.9
