gzalles/ambisonics-z-array/cad/max360/ada/3D-PDM-16CH/stl/sideB.stl

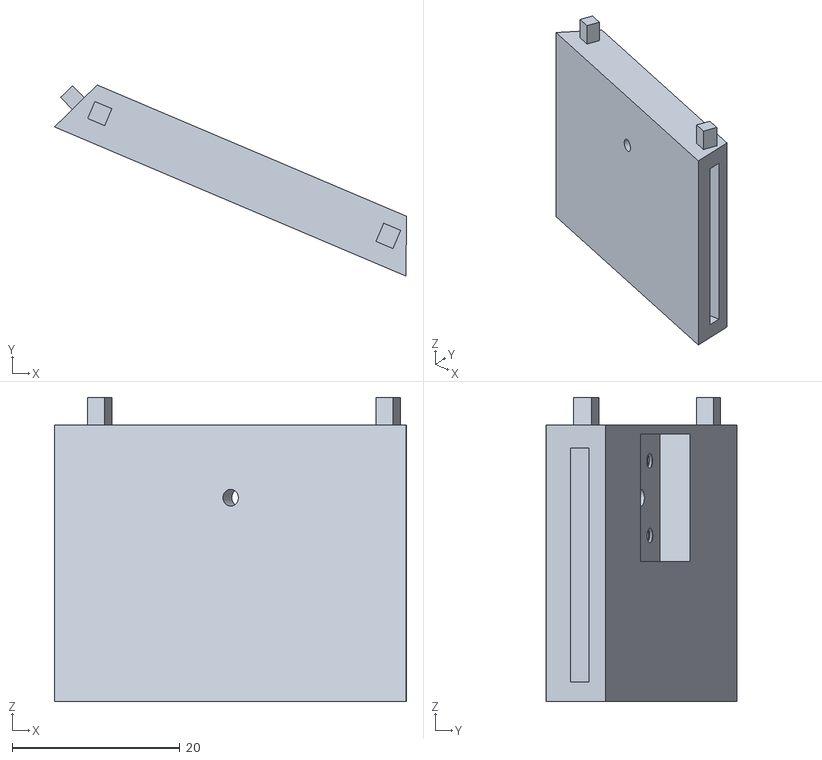
[picture p82: CAD file, 2023-04-07]
cad/max360/ada/3D-PDM-16CH/stl/sideB.stl
41.9 x 22.8 x 36.2
