gzalles/ambisonics-z-array/cad/msma-mch/sideB.stl

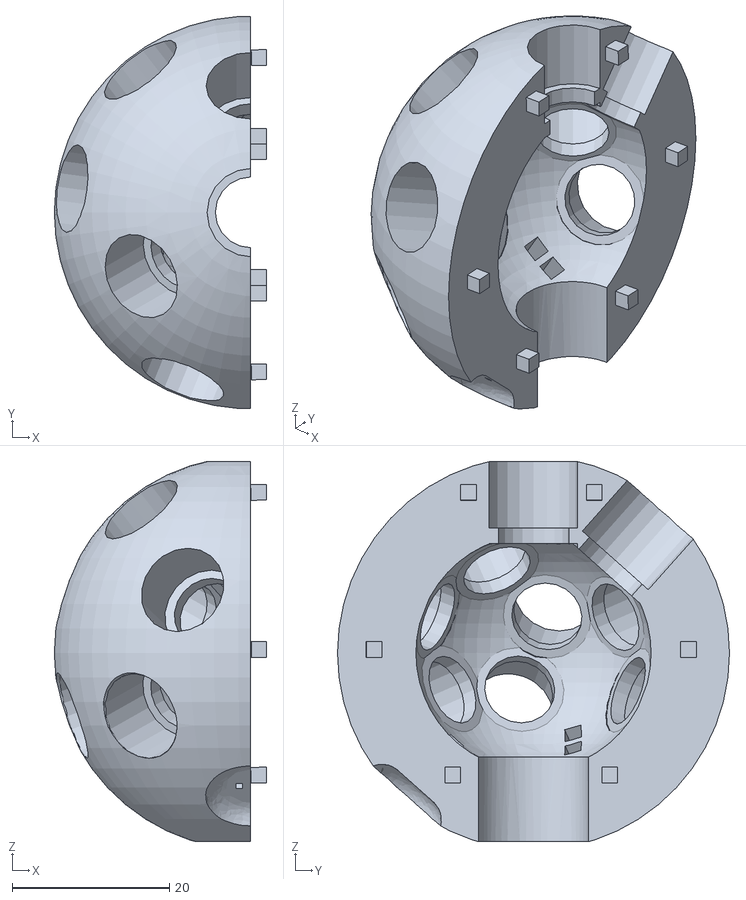
[picture p83: CAD file, 2023-04-07]
cad/msma-mch/sideB.stl
27.0 x 49.9 x 48.4
