gzalles/ambisonics-z-array/cad/octo/mch/cap-holder.stl

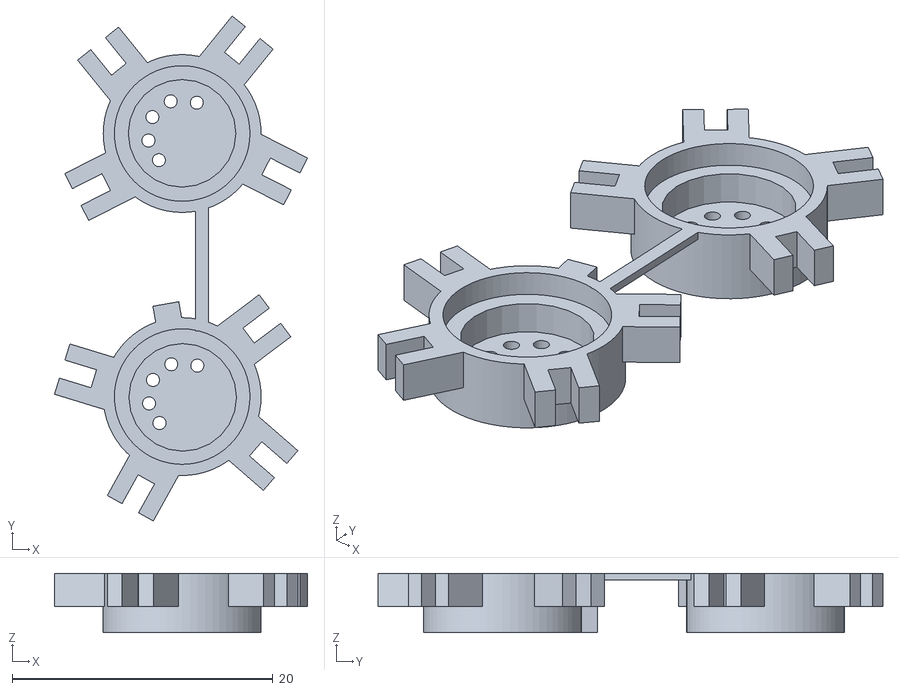
[picture p84: CAD file, 2023-04-07]
cad/octo/mch/cap-holder.stl
19.4 x 38.7 x 4.54
