gzalles/ambisonics-z-array/cad/octo/mch/prusa/detail.3mf

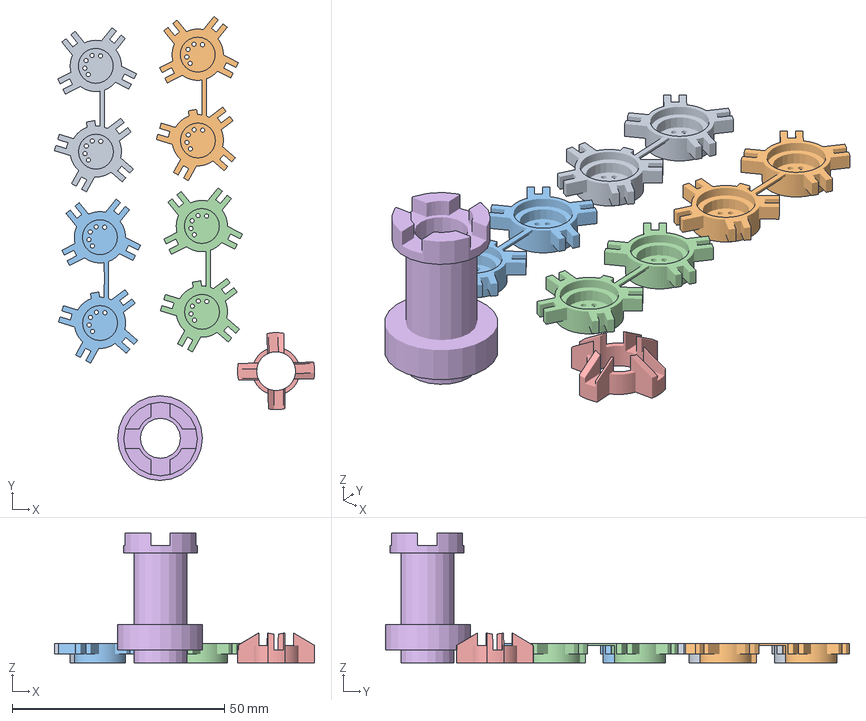
[picture p85: CAD file, 2023-04-07]
cad/octo/mch/prusa/detail.3mf
61.4 x 109.4 x 30.5 mm
cap-holder.stl x 4
connector.stl
neck.stl
