gzalles/ambisonics-z-array/cad/tiny/TinySpHEAR_bot.stl

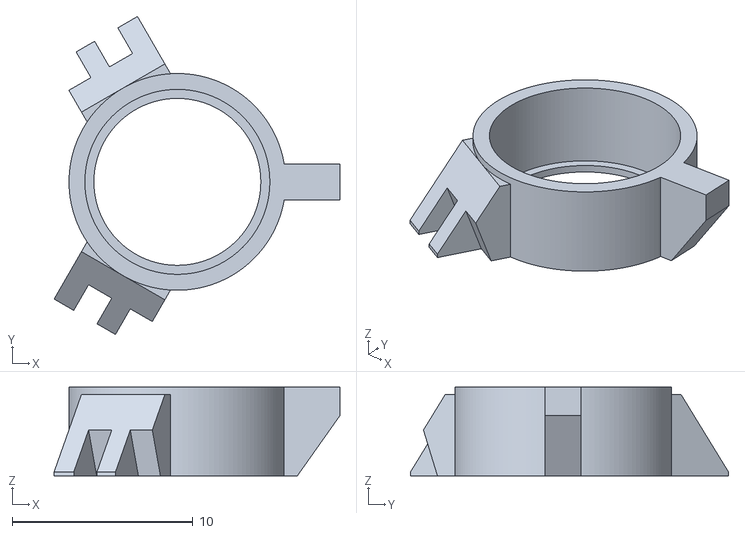
[picture p86: CAD file, 2023-04-07]
cad/tiny/TinySpHEAR_bot.stl
15.8 x 17.6 x 4.90
