gzalles/ambisonics-z-array/cad/bigSpHEAR_mems/big-3d-printed/filled-cap-holder.stl

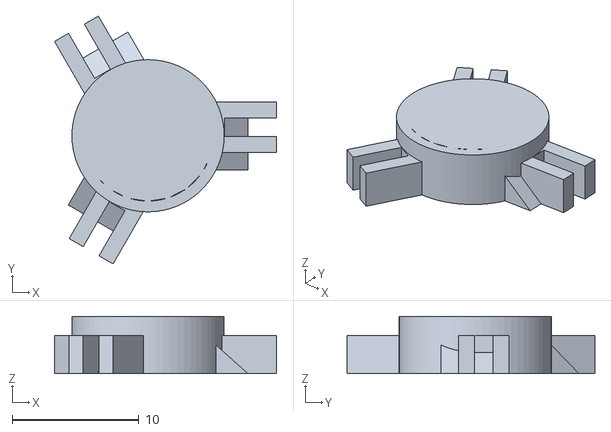
[picture p87: CAD file, 2023-04-07]
cad/bigSpHEAR_mems/big-3d-printed/filled-cap-holder.stl
17.5 x 19.5 x 4.50
