gzalles/ambisonics-z-array/cad/dl/msma/Handle.stl

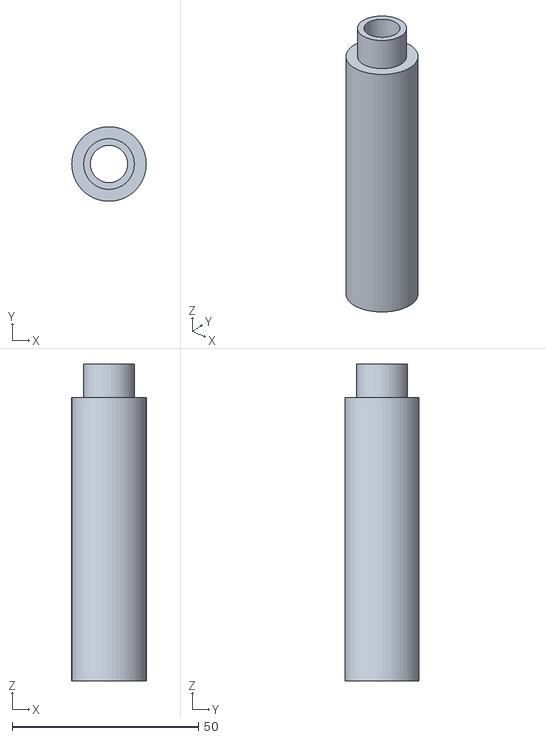
[picture p88: CAD file, 2023-04-07]
cad/dl/msma/Handle.stl
20.0 x 20.0 x 85.0
