gzalles/ambisonics-z-array/cad/max360/ada/3D-PDM-16CH/stl/top-center.stl

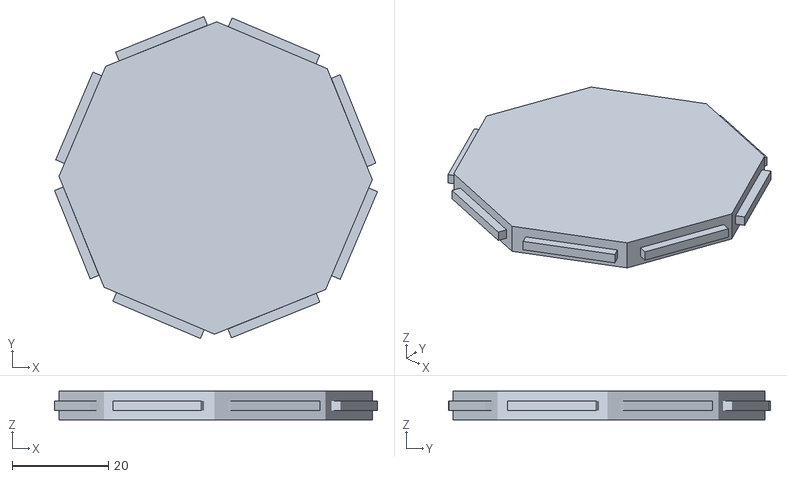
[picture p89: CAD file, 2023-04-07]
cad/max360/ada/3D-PDM-16CH/stl/top-center.stl
67.0 x 66.8 x 6.00
