gzalles/ambisonics-z-array/cad/max360/ada/3D-PDM-16CH/stl/bottom.stl

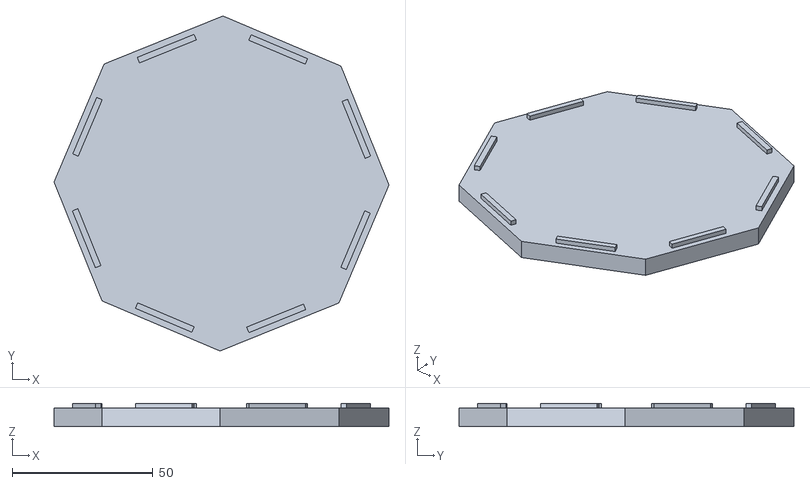
[picture p90: CAD file, 2023-04-07]
cad/max360/ada/3D-PDM-16CH/stl/bottom.stl
119.1 x 119.1 x 8.24
