gzalles/ambisonics-z-array/cad/msma-mch/capHolder16.stl

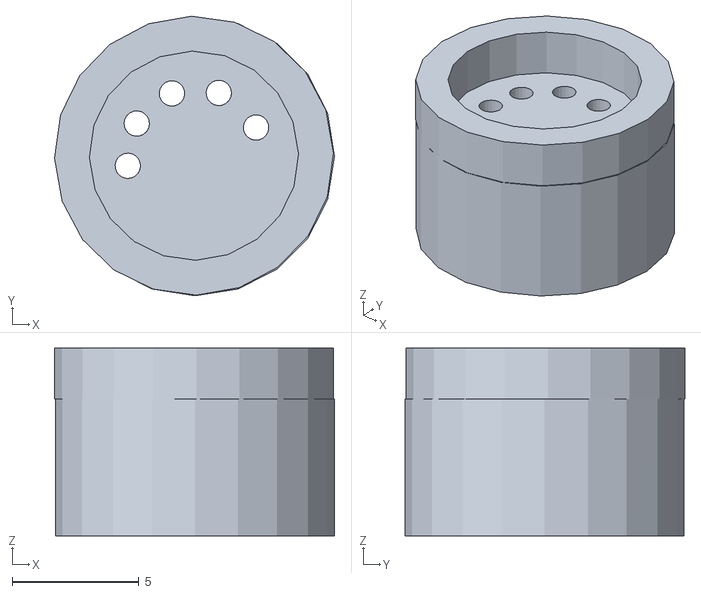
[picture p91: CAD file, 2023-04-07]
cad/msma-mch/capHolder16.stl
11.0 x 11.0 x 7.40
