gzalles/ambisonics-z-array/cad/octo/mch/connector.stl

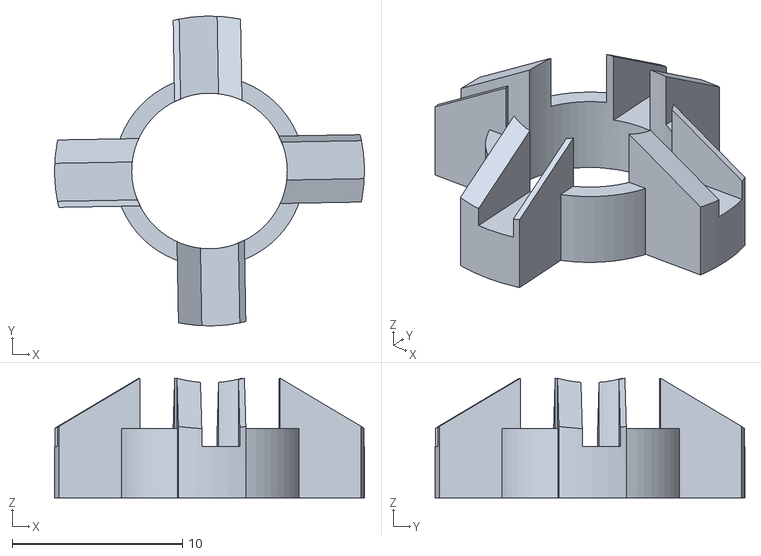
[picture p92: CAD file, 2023-04-07]
cad/octo/mch/connector.stl
18.2 x 18.2 x 7.03
