gzalles/ambisonics-z-array/cad/max360/ada/3D-PDM-16CH/stl/top-single.stl

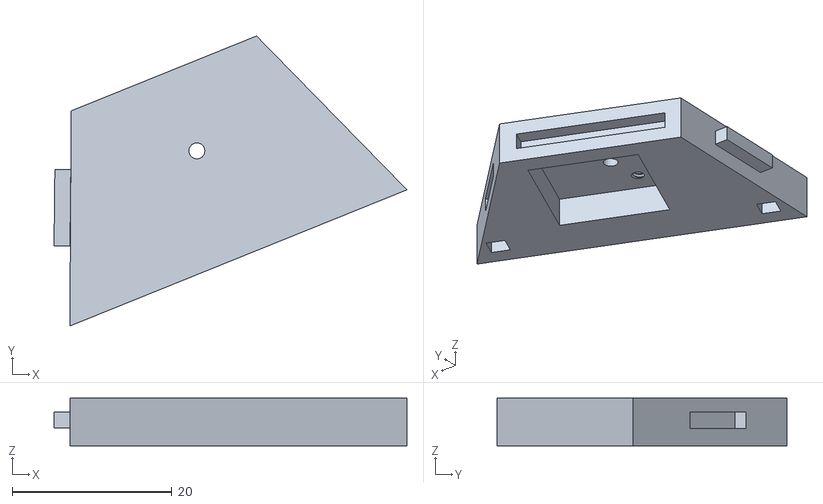
[picture p93: CAD file, 2023-04-07]
cad/max360/ada/3D-PDM-16CH/stl/top-single.stl
44.2 x 36.3 x 6.00
