gzalles/ambisonics-z-array/cad/msma-mch/noBody.3mf

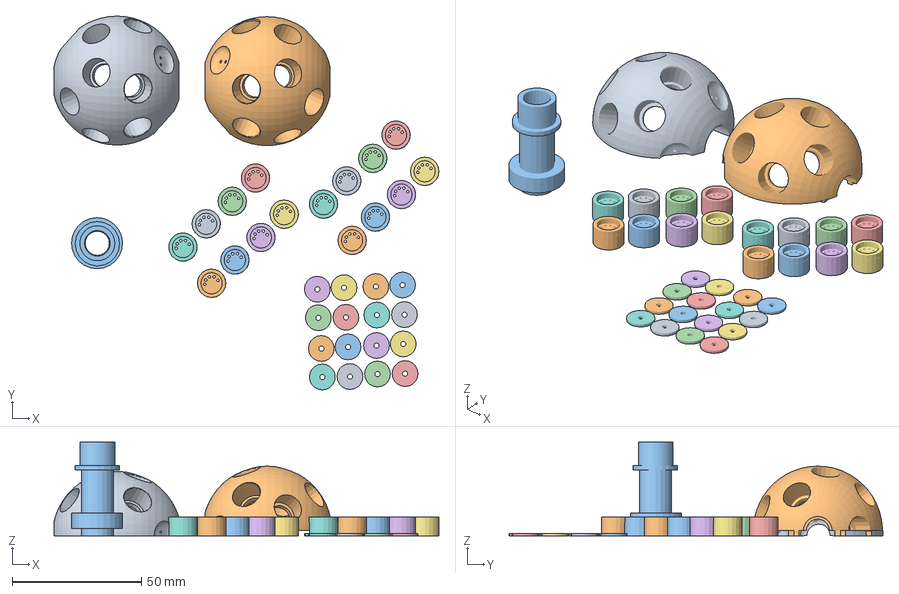
[picture p94: CAD file, 2023-04-07]
cad/msma-mch/noBody.3mf
148.9 x 144.6 x 36.4 mm
sideA.stl
sideB.stl
neck.stl
lid16.stl x 16
capHolder16.stl x 16
