gzalles/ambisonics-z-array/cad/msma-mch/sideA.stl

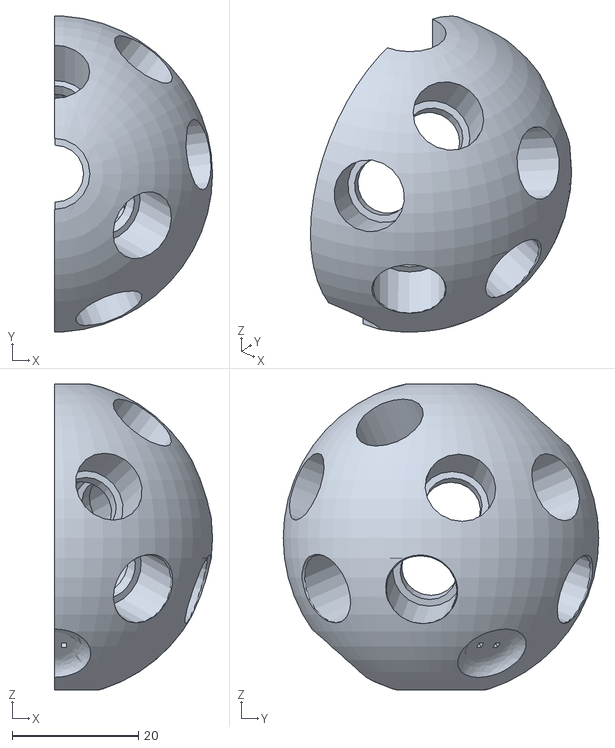
[picture p95: CAD file, 2023-04-07]
cad/msma-mch/sideA.stl
25.0 x 49.9 x 48.4
