gzalles/ambisonics-z-array/cad/max360/ada/3D-PDM-16CH/stl/perf-board-holder.stl

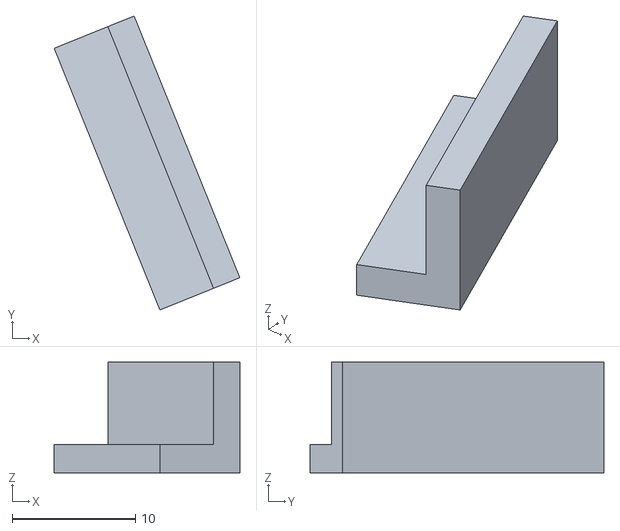
[picture p96: CAD file, 2023-04-07]
cad/max360/ada/3D-PDM-16CH/stl/perf-board-holder.stl
15.1 x 23.9 x 9.00
